peterheinrich/ZHAW_DFF_RPI_Network_Lab_Board/design/90-Ohm-Impedance.png

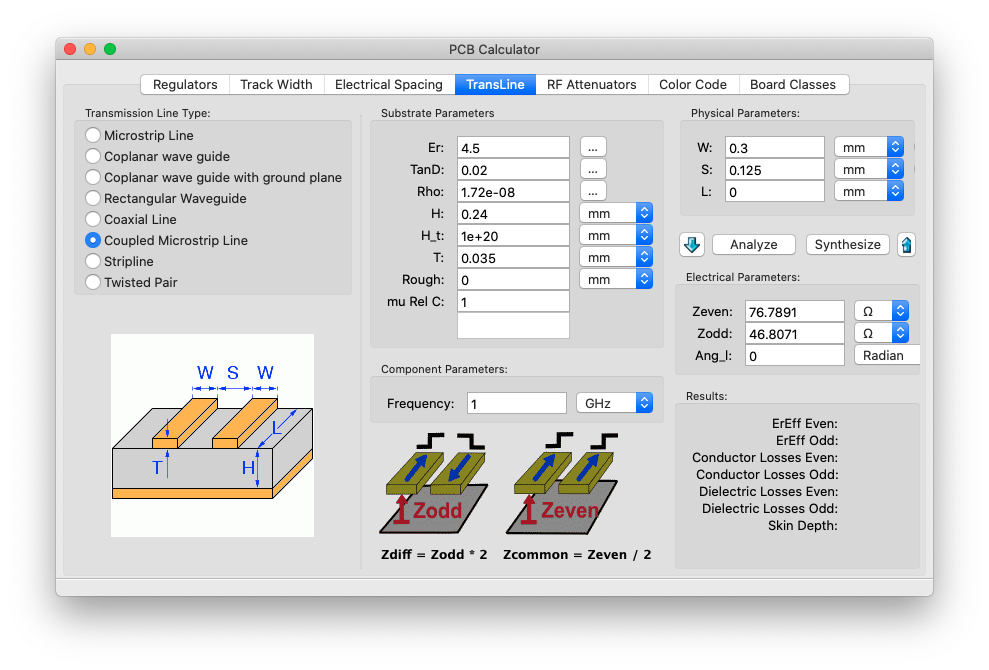
design/90-Ohm-Impedance.png
