peterheinrich/ZHAW_DFF_RPI_Network_Lab_Board/ecad/DSI.sch

## KiCad design ecad/DSI.sch (2020-12-07)

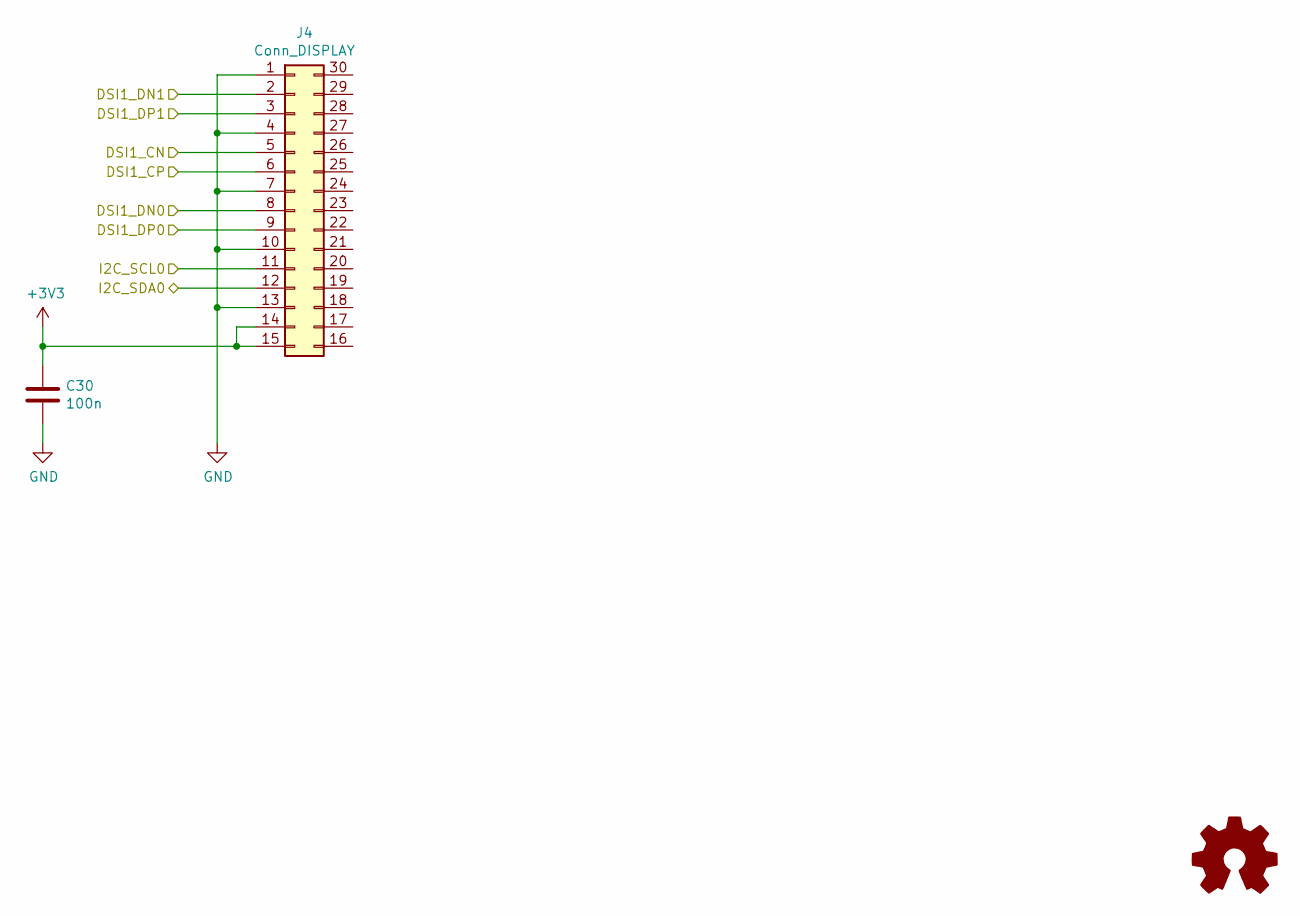
[picture p34: schematic DSI.sch]

Parts:
C30: 100n; C_0603_1608Metric; MPN C0603C104M4RACTU
J4: Conn_DISPLAY; 1-1734248-5; MPN 1-1734248-5

Connections:
+3V3: C30.1, J4.14, J4.15
DSI1_CN: J4.5
DSI1_CP: J4.6
DSI1_DN0: J4.8
DSI1_DN1: J4.2
DSI1_DP0: J4.9
DSI1_DP1: J4.3
GND: C30.2, J4.1, J4.4, J4.7, J4.10, J4.13
I2C_SCL0: J4.11
I2C_SDA0: J4.12
