peterheinrich/ZHAW_DFF_RPI_Network_Lab_Board/ecad/ETH0.sch

## KiCad design ecad/ETH0.sch (2020-12-07)

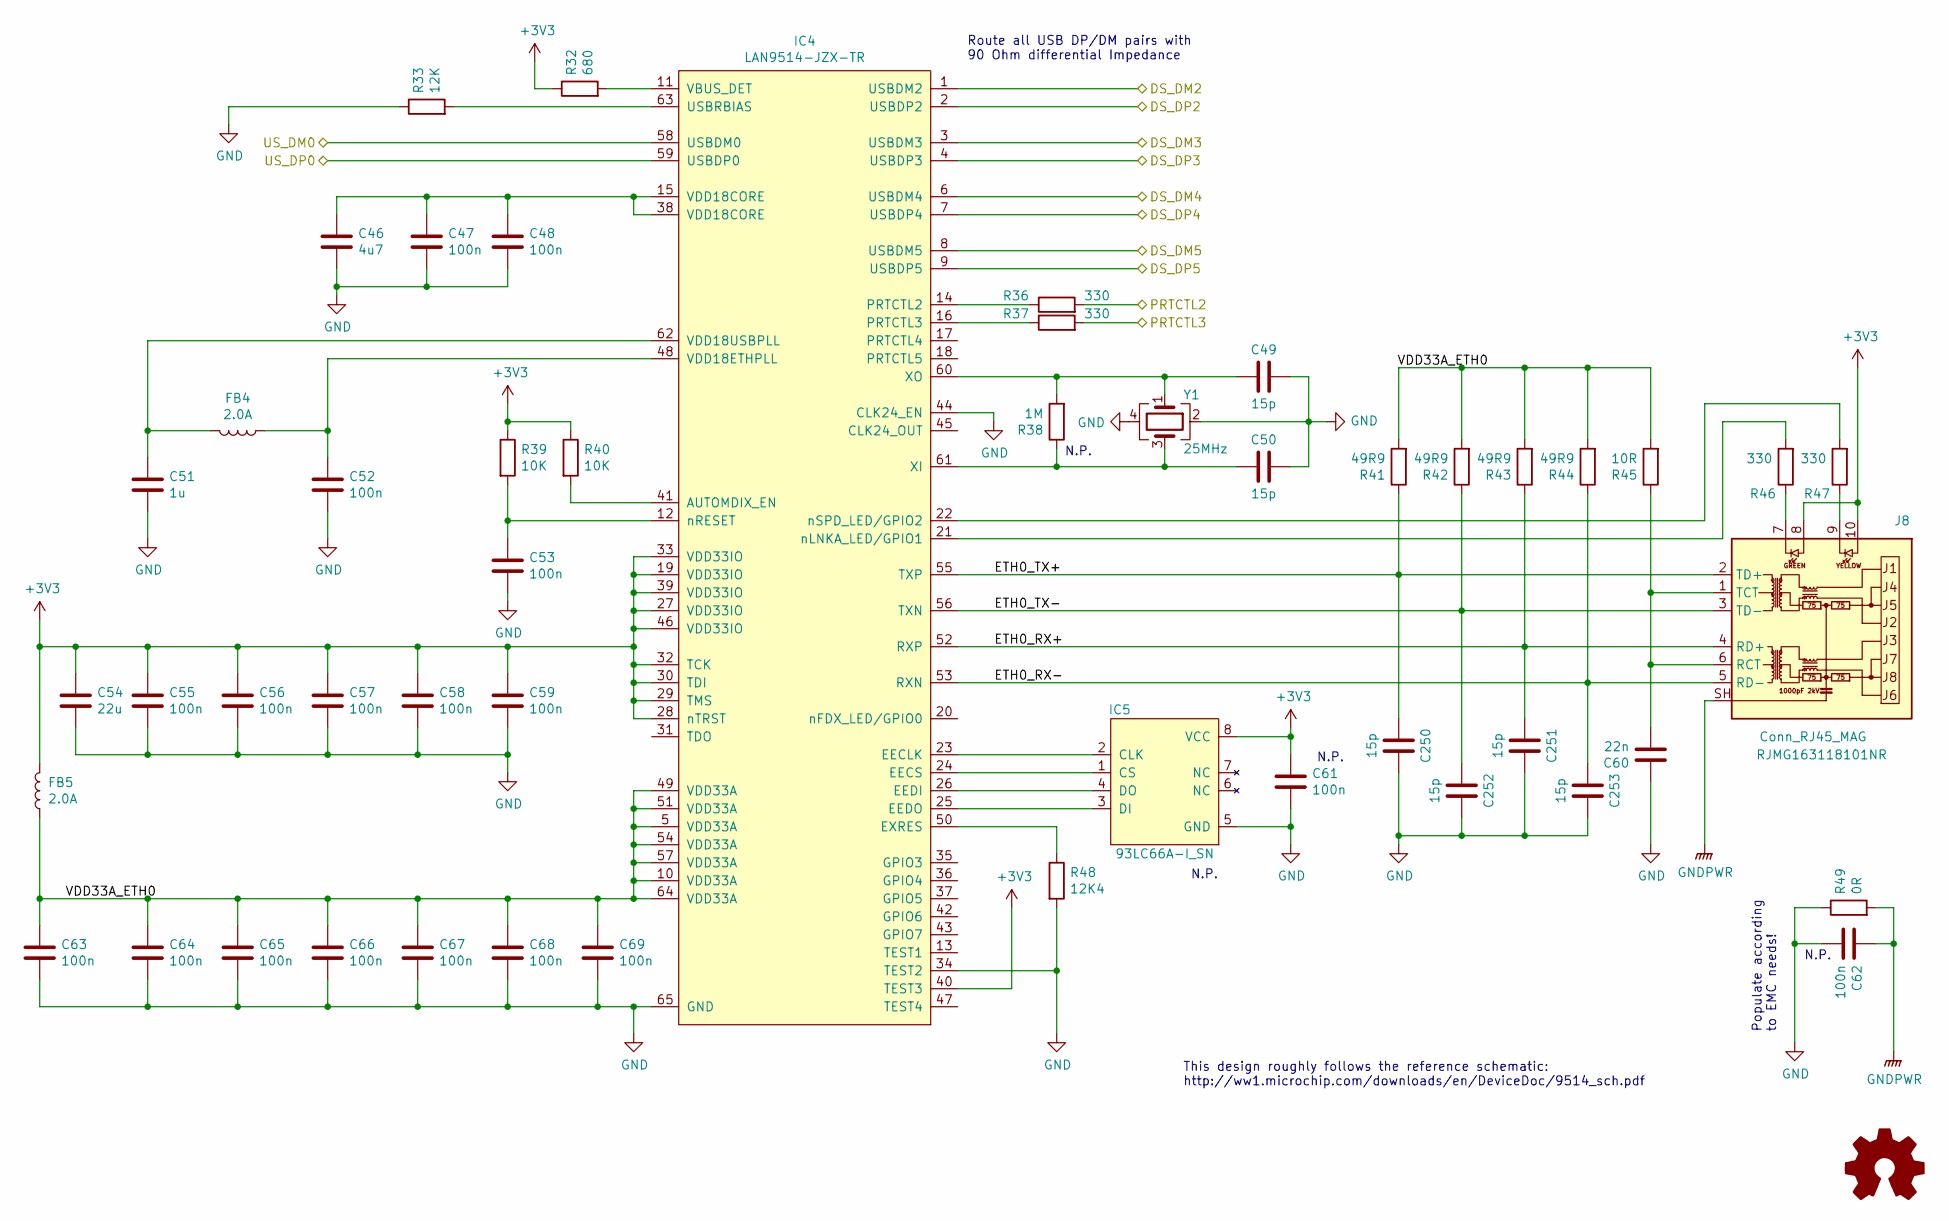
[picture p35: schematic ETH0.sch]

Parts:
C46: 4u7; C_0805_2012Metric; MPN GRM21BR61H475KE51L
C47, C48, C52, C53, C55, C56, C57, C58, C59, C61, C63, C64, C65, C66, C67, C68, C69: 100n; C_0603_1608Metric; MPN C0603C104M4RACTU
C49, C50, C250, C251, C252, C253: 15p; C_0603_1608Metric; MPN C0603C150J5GACTU
C51: 1u; C_0805_2012Metric; MPN C0805C105K3PACTU
C54: 22u; C_0805_2012Metric; MPN C0805C226M9PACTU
C60: 22n; C_0603_1608Metric; MPN C0603C223K1RACTU
C62: 100n; C_0805_2012Metric; MPN C0805C104K5RACTU
FB4, FB5: 2.0A; L_0603_1608Metric_Pad1.05x0.95mm_HandSolder; MPN BLM18PG121SN1D
IC4: LAN9514-JZX-TR; QFN-64-1EP_9x9mm_P0.5mm_EP7.15x7.15mm_ThermalVias; MPN LAN9514-JZX-TR
IC5: 93LC66A-I_SN; SOIC-8_3.9x4.9mm_P1.27mm; MPN 93LC66A-I_SN
J8: Conn_RJ45_MAG; RJMG163118101NR; MPN RJMG163118101NR
R32: 680; R_0603_1608Metric; MPN CRCW0603680RFKEA
R33: 12K; R_0603_1608Metric; MPN CRCW060312K0FKEA
R36, R37, R46, R47: 330; R_0603_1608Metric; MPN CRCW0603330RFKEA
R38: 1M; R_0603_1608Metric; MPN CRCW06031M00FKEA
R39, R40: 10K; R_0603_1608Metric; MPN CRCW060310K0FKEA
R41, R42, R43, R44: 49R9; R_0603_1608Metric; MPN CRCW060349R9FKEA
R45: 10R; R_0603_1608Metric; MPN CRCW060310R0FKEA
R48: 12K4; R_0603_1608Metric; MPN CRCW060312K4FKEA
R49: 0R; R_0805_2012Metric; MPN CRCW08050000Z0EA
Y1: 25MHz; Crystal_SMD_Abracon_ABM8G-4Pin_3.2x2.5mm; MPN LFXTAL055299

Connections:
+3V3: C54.1, C55.1, C56.1, C57.1, C58.1, C59.1, C61.1, FB5.2, IC4.19 (VDD33IO), IC4.27 (VDD33IO), IC4.28 (nTRST), IC4.29 (TMS), IC4.30 (TDI), IC4.32 (TCK), IC4.33 (VDD33IO), IC4.39 (VDD33IO), IC4.40 (TEST3), IC4.46 (VDD33IO), IC5.8 (VCC), J8.8, J8.10, R32.1, R39.1, R40.1
DS_DM2: IC4.1 (USBDM2)
DS_DM3: IC4.3 (USBDM3)
DS_DM4: IC4.6 (USBDM4)
DS_DM5: IC4.8 (USBDM5)
DS_DP2: IC4.2 (USBDP2)
DS_DP3: IC4.4 (USBDP3)
DS_DP4: IC4.7 (USBDP4)
DS_DP5: IC4.9 (USBDP5)
ETH0_RX+: C251.2, IC4.52 (RXP), J8.4 (RD+), R43.1
ETH0_RX-: C253.2, IC4.53 (RXN), J8.5 (RD-), R44.1
ETH0_TX+: C250.2, IC4.55 (TXP), J8.2 (TD+), R41.1
ETH0_TX-: C252.2, IC4.56 (TXN), J8.3 (TD-), R42.1
GND: C46.2, C47.2, C48.2, C49.1, C50.1, C51.2, C52.2, C53.2, C54.2, C55.2, C56.2, C57.2, C58.2, C59.2, C60.1, C61.2, C62.2, C63.2, C64.2, C65.2, C66.2, C67.2, C68.2, C69.2, C250.1, C251.1, C252.1, C253.1, IC4.34 (TEST2), IC4.44 (CLK24_EN), IC4.65 (GND), IC5.5 (GND), R33.1, R48.2, R49.1, Y1.2, Y1.4
GNDPWR: C62.1, J8.SH, R49.2
unnamed: C46.1, C47.1, C48.1, IC4.15 (VDD18CORE), IC4.38 (VDD18CORE)
unnamed: C49.2, IC4.60 (XO), R38.2, Y1.1
unnamed: C50.2, IC4.61 (XI), R38.1, Y1.3
unnamed: C51.1, FB4.2, IC4.62 (VDD18USBPLL)
unnamed: C52.1, FB4.1, IC4.48 (VDD18ETHPLL)
unnamed: C53.1, IC4.12 (nRESET), R39.2
unnamed: C60.2, J8.1 (TCT), J8.6 (RCT), R45.1
unnamed: IC4.11 (VBUS_DET), R32.2
unnamed: IC4.14 (PRTCTL2), R36.1
unnamed: IC4.16 (PRTCTL3), R37.1
unnamed: IC4.21 (nLNKA_LED/GPIO1), R46.2
unnamed: IC4.22 (nSPD_LED/GPIO2), R47.2
unnamed: IC4.23 (EECLK), IC5.2 (CLK)
unnamed: IC4.24 (EECS), IC5.1 (CS)
unnamed: IC4.25 (EEDO), IC5.3 (DI)
unnamed: IC4.26 (EEDI), IC5.4 (DO)
unnamed: IC4.41 (AUTOMDIX_EN), R40.2
unnamed: IC4.50 (EXRES), R48.1
unnamed: IC4.63 (USBRBIAS), R33.2
unnamed: J8.7, R46.1
unnamed: J8.9, R47.1
PRTCTL2: R36.2
PRTCTL3: R37.2
US_DM0: IC4.58 (USBDM0)
US_DP0: IC4.59 (USBDP0)
VDD33A_ETH0: C63.1, C64.1, C65.1, C66.1, C67.1, C68.1, C69.1, FB5.1, IC4.5 (VDD33A), IC4.10 (VDD33A), IC4.49 (VDD33A), IC4.51 (VDD33A), IC4.54 (VDD33A), IC4.57 (VDD33A), IC4.64 (VDD33A), R41.2, R42.2, R43.2, R44.2, R45.2

Notes on the sheet:
N.P.
Route all USB DP/DM pairs with 90 Ohm differential Impedance
This design roughly follows the reference schematic: http://ww1.microchip.com/downloads/en/DeviceDoc/9514_sch.pdf
Populate according to EMC needs!
