peterheinrich/ZHAW_DFF_RPI_Network_Lab_Board/ecad/ETH1.sch

## KiCad design ecad/ETH1.sch (2020-12-07)

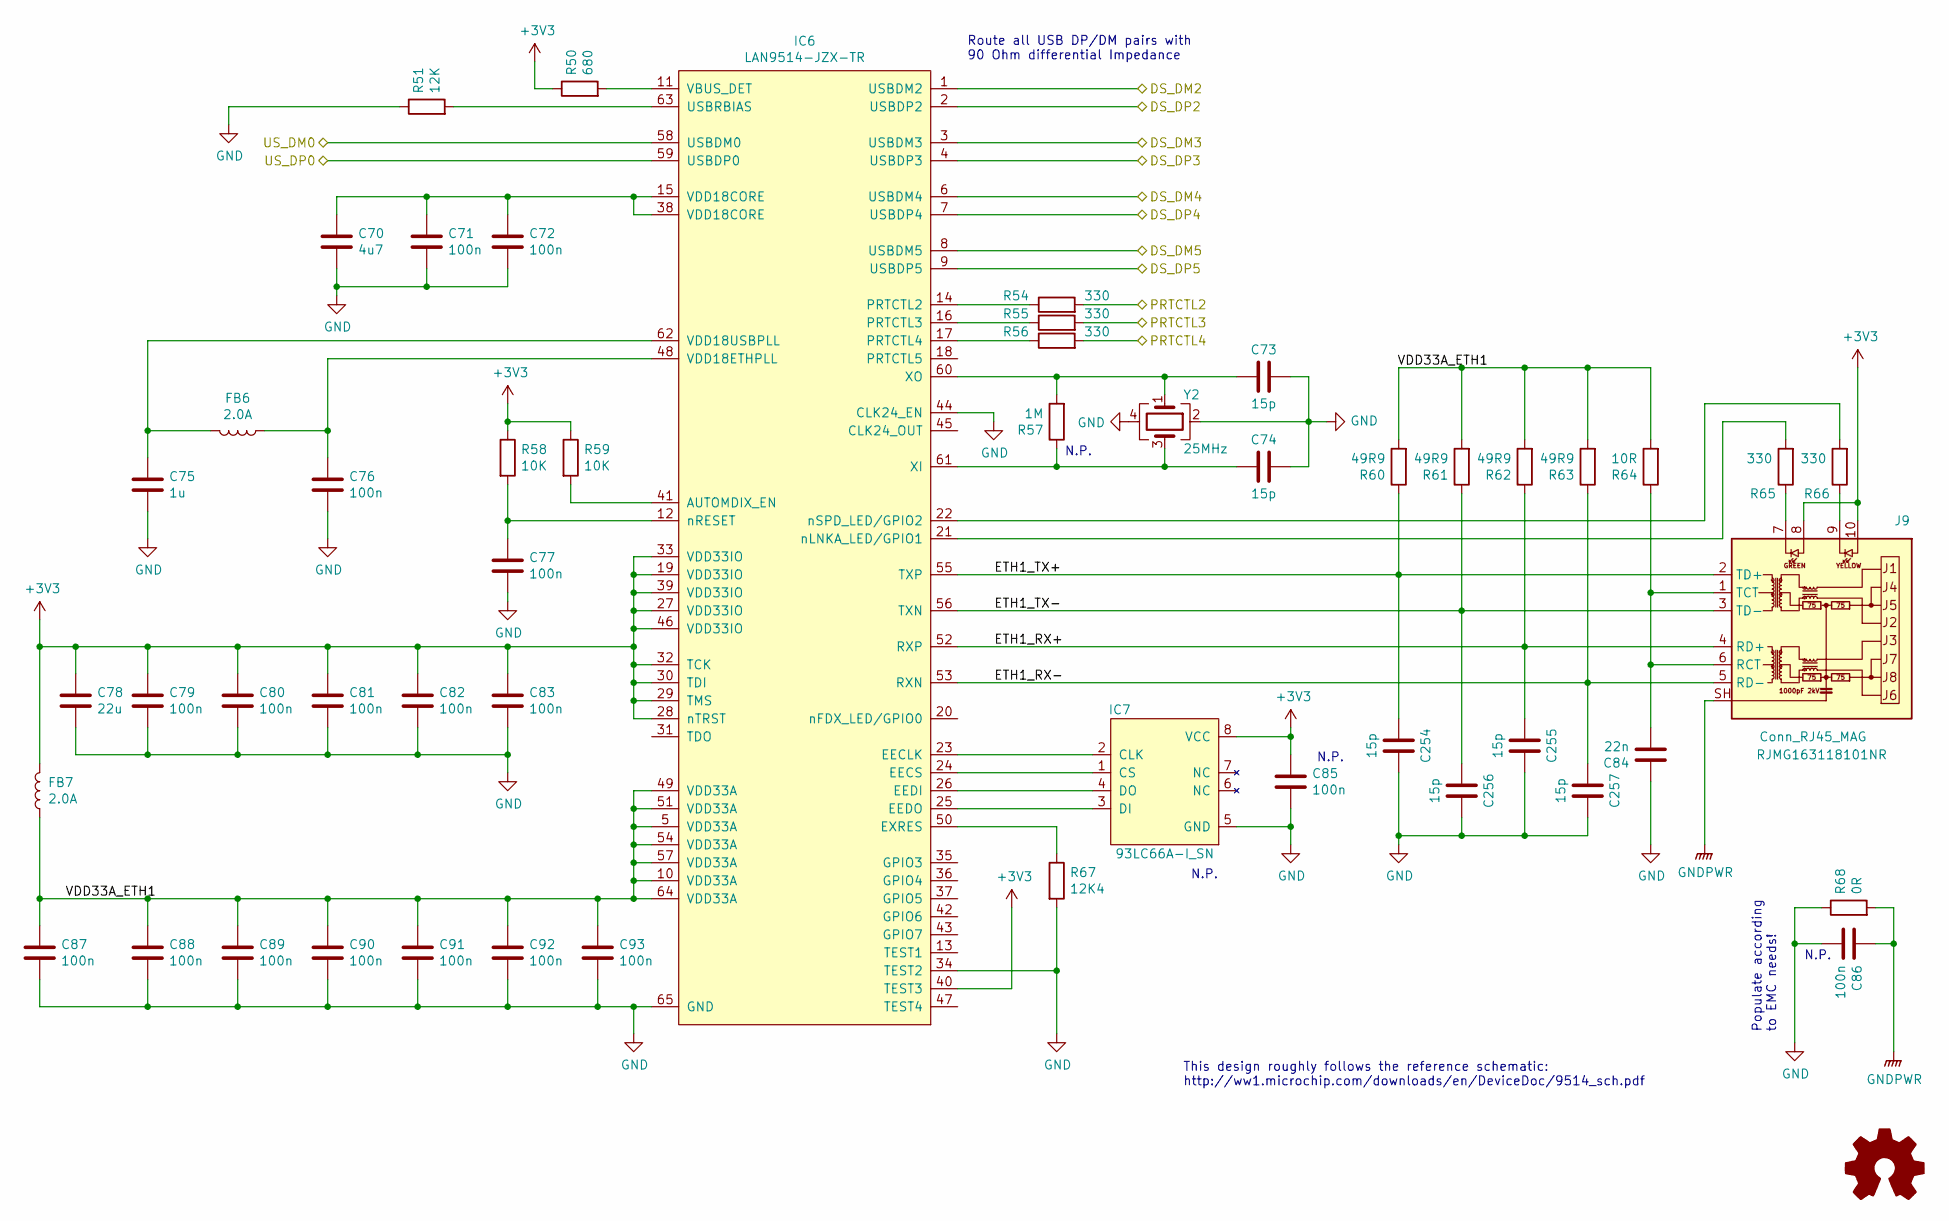
[picture p36: schematic ETH1.sch]

Parts:
C70: 4u7; C_0805_2012Metric; MPN GRM21BR61H475KE51L
C71, C72, C76, C77, C79, C80, C81, C82, C83, C85, C87, C88, C89, C90, C91, C92, C93: 100n; C_0603_1608Metric; MPN C0603C104M4RACTU
C73, C74, C254, C255, C256, C257: 15p; C_0603_1608Metric; MPN C0603C150J5GACTU
C75: 1u; C_0805_2012Metric; MPN C0805C105K3PACTU
C78: 22u; C_0805_2012Metric; MPN C0805C226M9PACTU
C84: 22n; C_0603_1608Metric; MPN C0603C223K1RACTU
C86: 100n; C_0805_2012Metric; MPN C0805C104K5RACTU
FB6, FB7: 2.0A; L_0603_1608Metric_Pad1.05x0.95mm_HandSolder; MPN BLM18PG121SN1D
IC6: LAN9514-JZX-TR; QFN-64-1EP_9x9mm_P0.5mm_EP7.15x7.15mm_ThermalVias; MPN LAN9514-JZX-TR
IC7: 93LC66A-I_SN; SOIC-8_3.9x4.9mm_P1.27mm; MPN 93LC66A-I_SN
J9: Conn_RJ45_MAG; RJMG163118101NR; MPN RJMG163118101NR
R50: 680; R_0603_1608Metric; MPN CRCW0603680RFKEA
R51: 12K; R_0603_1608Metric; MPN CRCW060312K0FKEA
R54, R55, R56, R65, R66: 330; R_0603_1608Metric; MPN CRCW0603330RFKEA
R57: 1M; R_0603_1608Metric; MPN CRCW06031M00FKEA
R58, R59: 10K; R_0603_1608Metric; MPN CRCW060310K0FKEA
R60, R61, R62, R63: 49R9; R_0603_1608Metric; MPN CRCW060349R9FKEA
R64: 10R; R_0603_1608Metric; MPN CRCW060310R0FKEA
R67: 12K4; R_0603_1608Metric; MPN CRCW060312K4FKEA
R68: 0R; R_0805_2012Metric; MPN CRCW08050000Z0EA
Y2: 25MHz; Crystal_SMD_Abracon_ABM8G-4Pin_3.2x2.5mm; MPN LFXTAL055299

Connections:
+3V3: C78.1, C79.1, C80.1, C81.1, C82.1, C83.1, C85.1, FB7.2, IC6.19 (VDD33IO), IC6.27 (VDD33IO), IC6.28 (nTRST), IC6.29 (TMS), IC6.30 (TDI), IC6.32 (TCK), IC6.33 (VDD33IO), IC6.39 (VDD33IO), IC6.40 (TEST3), IC6.46 (VDD33IO), IC7.8 (VCC), J9.8, J9.10, R50.1, R58.1, R59.1
DS_DM2: IC6.1 (USBDM2)
DS_DM3: IC6.3 (USBDM3)
DS_DM4: IC6.6 (USBDM4)
DS_DM5: IC6.8 (USBDM5)
DS_DP2: IC6.2 (USBDP2)
DS_DP3: IC6.4 (USBDP3)
DS_DP4: IC6.7 (USBDP4)
DS_DP5: IC6.9 (USBDP5)
ETH1_RX+: C255.2, IC6.52 (RXP), J9.4 (RD+), R62.1
ETH1_RX-: C257.2, IC6.53 (RXN), J9.5 (RD-), R63.1
ETH1_TX+: C254.2, IC6.55 (TXP), J9.2 (TD+), R60.1
ETH1_TX-: C256.2, IC6.56 (TXN), J9.3 (TD-), R61.1
GND: C70.2, C71.2, C72.2, C73.1, C74.1, C75.2, C76.2, C77.2, C78.2, C79.2, C80.2, C81.2, C82.2, C83.2, C84.1, C85.2, C86.2, C87.2, C88.2, C89.2, C90.2, C91.2, C92.2, C93.2, C254.1, C255.1, C256.1, C257.1, IC6.34 (TEST2), IC6.44 (CLK24_EN), IC6.65 (GND), IC7.5 (GND), R51.1, R67.2, R68.1, Y2.2, Y2.4
GNDPWR: C86.1, J9.SH, R68.2
unnamed: C70.1, C71.1, C72.1, IC6.15 (VDD18CORE), IC6.38 (VDD18CORE)
unnamed: C73.2, IC6.60 (XO), R57.2, Y2.1
unnamed: C74.2, IC6.61 (XI), R57.1, Y2.3
unnamed: C75.1, FB6.2, IC6.62 (VDD18USBPLL)
unnamed: C76.1, FB6.1, IC6.48 (VDD18ETHPLL)
unnamed: C77.1, IC6.12 (nRESET), R58.2
unnamed: C84.2, J9.1 (TCT), J9.6 (RCT), R64.1
unnamed: IC6.11 (VBUS_DET), R50.2
unnamed: IC6.14 (PRTCTL2), R54.1
unnamed: IC6.16 (PRTCTL3), R55.1
unnamed: IC6.17 (PRTCTL4), R56.1
unnamed: IC6.21 (nLNKA_LED/GPIO1), R65.2
unnamed: IC6.22 (nSPD_LED/GPIO2), R66.2
unnamed: IC6.23 (EECLK), IC7.2 (CLK)
unnamed: IC6.24 (EECS), IC7.1 (CS)
unnamed: IC6.25 (EEDO), IC7.3 (DI)
unnamed: IC6.26 (EEDI), IC7.4 (DO)
unnamed: IC6.41 (AUTOMDIX_EN), R59.2
unnamed: IC6.50 (EXRES), R67.1
unnamed: IC6.63 (USBRBIAS), R51.2
unnamed: J9.7, R65.1
unnamed: J9.9, R66.1
PRTCTL2: R54.2
PRTCTL3: R55.2
PRTCTL4: R56.2
US_DM0: IC6.58 (USBDM0)
US_DP0: IC6.59 (USBDP0)
VDD33A_ETH1: C87.1, C88.1, C89.1, C90.1, C91.1, C92.1, C93.1, FB7.1, IC6.5 (VDD33A), IC6.10 (VDD33A), IC6.49 (VDD33A), IC6.51 (VDD33A), IC6.54 (VDD33A), IC6.57 (VDD33A), IC6.64 (VDD33A), R60.2, R61.2, R62.2, R63.2, R64.2

Notes on the sheet:
N.P.
Route all USB DP/DM pairs with 90 Ohm differential Impedance
This design roughly follows the reference schematic: http://ww1.microchip.com/downloads/en/DeviceDoc/9514_sch.pdf
Populate according to EMC needs!
