peterheinrich/ZHAW_DFF_RPI_Network_Lab_Board/ecad/ETH2.sch

## KiCad design ecad/ETH2.sch (2020-12-07)

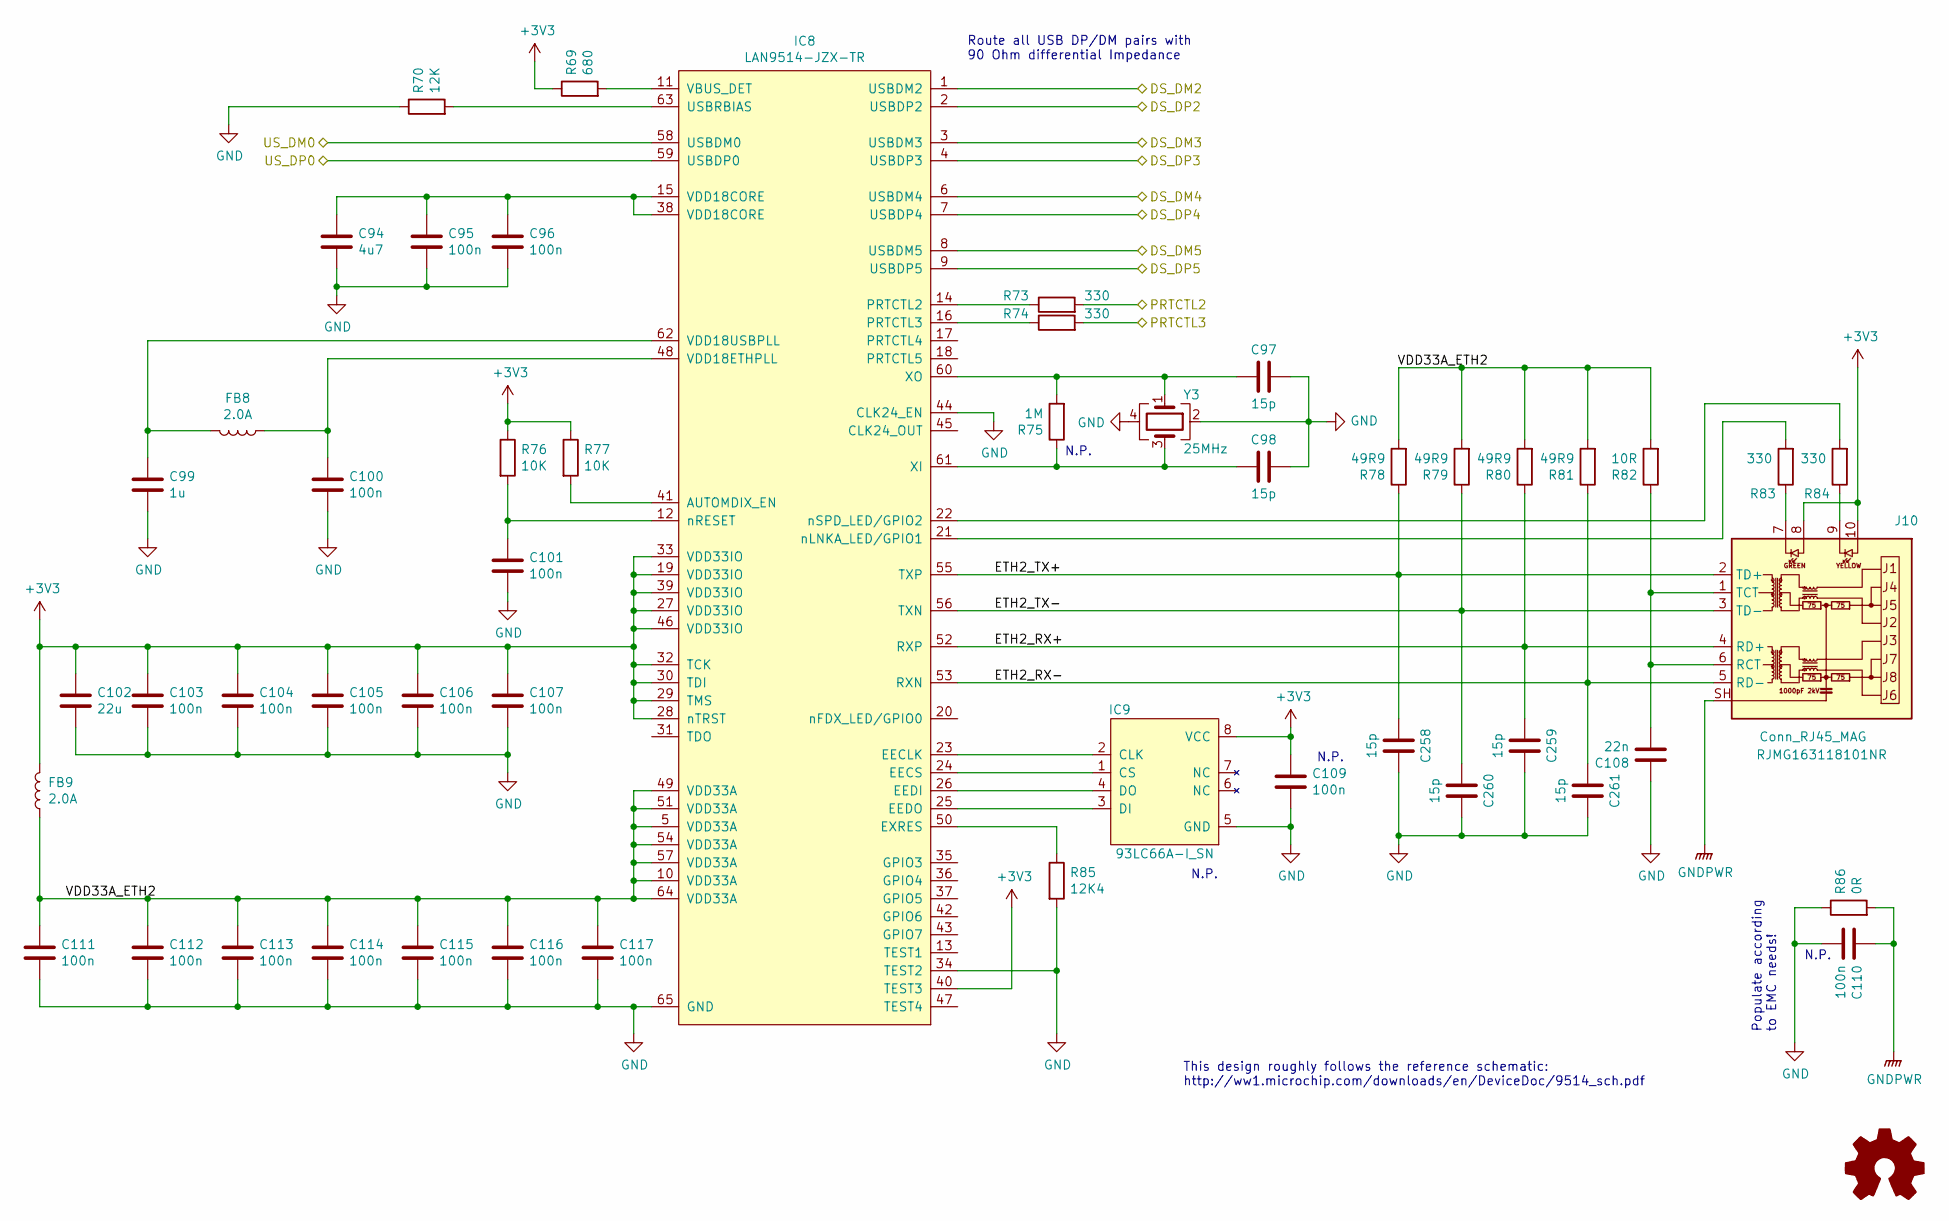
[picture p37: schematic ETH2.sch]

Parts:
C94: 4u7; C_0805_2012Metric; MPN GRM21BR61H475KE51L
C95, C96, C100, C101, C103, C104, C105, C106, C107, C109, C111, C112, C113, C114, C115, C116, C117: 100n; C_0603_1608Metric; MPN C0603C104M4RACTU
C97, C98, C258, C259, C260, C261: 15p; C_0603_1608Metric; MPN C0603C150J5GACTU
C99: 1u; C_0805_2012Metric; MPN C0805C105K3PACTU
C102: 22u; C_0805_2012Metric; MPN C0805C226M9PACTU
C108: 22n; C_0603_1608Metric; MPN C0603C223K1RACTU
C110: 100n; C_0805_2012Metric; MPN C0805C104K5RACTU
FB8, FB9: 2.0A; L_0603_1608Metric_Pad1.05x0.95mm_HandSolder; MPN BLM18PG121SN1D
IC8: LAN9514-JZX-TR; QFN-64-1EP_9x9mm_P0.5mm_EP7.15x7.15mm_ThermalVias; MPN LAN9514-JZX-TR
IC9: 93LC66A-I_SN; SOIC-8_3.9x4.9mm_P1.27mm; MPN 93LC66A-I_SN
J10: Conn_RJ45_MAG; RJMG163118101NR; MPN RJMG163118101NR
R69: 680; R_0603_1608Metric; MPN CRCW0603680RFKEA
R70: 12K; R_0603_1608Metric; MPN CRCW060312K0FKEA
R73, R74, R83, R84: 330; R_0603_1608Metric; MPN CRCW0603330RFKEA
R75: 1M; R_0603_1608Metric; MPN CRCW06031M00FKEA
R76, R77: 10K; R_0603_1608Metric; MPN CRCW060310K0FKEA
R78, R79, R80, R81: 49R9; R_0603_1608Metric; MPN CRCW060349R9FKEA
R82: 10R; R_0603_1608Metric; MPN CRCW060310R0FKEA
R85: 12K4; R_0603_1608Metric; MPN CRCW060312K4FKEA
R86: 0R; R_0805_2012Metric; MPN CRCW08050000Z0EA
Y3: 25MHz; Crystal_SMD_Abracon_ABM8G-4Pin_3.2x2.5mm; MPN LFXTAL055299

Connections:
+3V3: C102.1, C103.1, C104.1, C105.1, C106.1, C107.1, C109.1, FB9.2, IC8.19 (VDD33IO), IC8.27 (VDD33IO), IC8.28 (nTRST), IC8.29 (TMS), IC8.30 (TDI), IC8.32 (TCK), IC8.33 (VDD33IO), IC8.39 (VDD33IO), IC8.40 (TEST3), IC8.46 (VDD33IO), IC9.8 (VCC), J10.8, J10.10, R69.1, R76.1, R77.1
DS_DM2: IC8.1 (USBDM2)
DS_DM3: IC8.3 (USBDM3)
DS_DM4: IC8.6 (USBDM4)
DS_DM5: IC8.8 (USBDM5)
DS_DP2: IC8.2 (USBDP2)
DS_DP3: IC8.4 (USBDP3)
DS_DP4: IC8.7 (USBDP4)
DS_DP5: IC8.9 (USBDP5)
ETH2_RX+: C259.2, IC8.52 (RXP), J10.4 (RD+), R80.1
ETH2_RX-: C261.2, IC8.53 (RXN), J10.5 (RD-), R81.1
ETH2_TX+: C258.2, IC8.55 (TXP), J10.2 (TD+), R78.1
ETH2_TX-: C260.2, IC8.56 (TXN), J10.3 (TD-), R79.1
GND: C94.2, C95.2, C96.2, C97.1, C98.1, C99.2, C100.2, C101.2, C102.2, C103.2, C104.2, C105.2, C106.2, C107.2, C108.1, C109.2, C110.2, C111.2, C112.2, C113.2, C114.2, C115.2, C116.2, C117.2, C258.1, C259.1, C260.1, C261.1, IC8.34 (TEST2), IC8.44 (CLK24_EN), IC8.65 (GND), IC9.5 (GND), R70.1, R85.2, R86.1, Y3.2, Y3.4
GNDPWR: C110.1, J10.SH, R86.2
unnamed: C94.1, C95.1, C96.1, IC8.15 (VDD18CORE), IC8.38 (VDD18CORE)
unnamed: C97.2, IC8.60 (XO), R75.2, Y3.1
unnamed: C98.2, IC8.61 (XI), R75.1, Y3.3
unnamed: C99.1, FB8.2, IC8.62 (VDD18USBPLL)
unnamed: C100.1, FB8.1, IC8.48 (VDD18ETHPLL)
unnamed: C101.1, IC8.12 (nRESET), R76.2
unnamed: C108.2, J10.1 (TCT), J10.6 (RCT), R82.1
unnamed: IC8.11 (VBUS_DET), R69.2
unnamed: IC8.14 (PRTCTL2), R73.1
unnamed: IC8.16 (PRTCTL3), R74.1
unnamed: IC8.21 (nLNKA_LED/GPIO1), R83.2
unnamed: IC8.22 (nSPD_LED/GPIO2), R84.2
unnamed: IC8.23 (EECLK), IC9.2 (CLK)
unnamed: IC8.24 (EECS), IC9.1 (CS)
unnamed: IC8.25 (EEDO), IC9.3 (DI)
unnamed: IC8.26 (EEDI), IC9.4 (DO)
unnamed: IC8.41 (AUTOMDIX_EN), R77.2
unnamed: IC8.50 (EXRES), R85.1
unnamed: IC8.63 (USBRBIAS), R70.2
unnamed: J10.7, R83.1
unnamed: J10.9, R84.1
PRTCTL2: R73.2
PRTCTL3: R74.2
US_DM0: IC8.58 (USBDM0)
US_DP0: IC8.59 (USBDP0)
VDD33A_ETH2: C111.1, C112.1, C113.1, C114.1, C115.1, C116.1, C117.1, FB9.1, IC8.5 (VDD33A), IC8.10 (VDD33A), IC8.49 (VDD33A), IC8.51 (VDD33A), IC8.54 (VDD33A), IC8.57 (VDD33A), IC8.64 (VDD33A), R78.2, R79.2, R80.2, R81.2, R82.2

Notes on the sheet:
N.P.
Route all USB DP/DM pairs with 90 Ohm differential Impedance
This design roughly follows the reference schematic: http://ww1.microchip.com/downloads/en/DeviceDoc/9514_sch.pdf
Populate according to EMC needs!
