peterheinrich/ZHAW_DFF_RPI_Network_Lab_Board/ecad/HDMI.sch

## KiCad design ecad/HDMI.sch (2020-12-07)

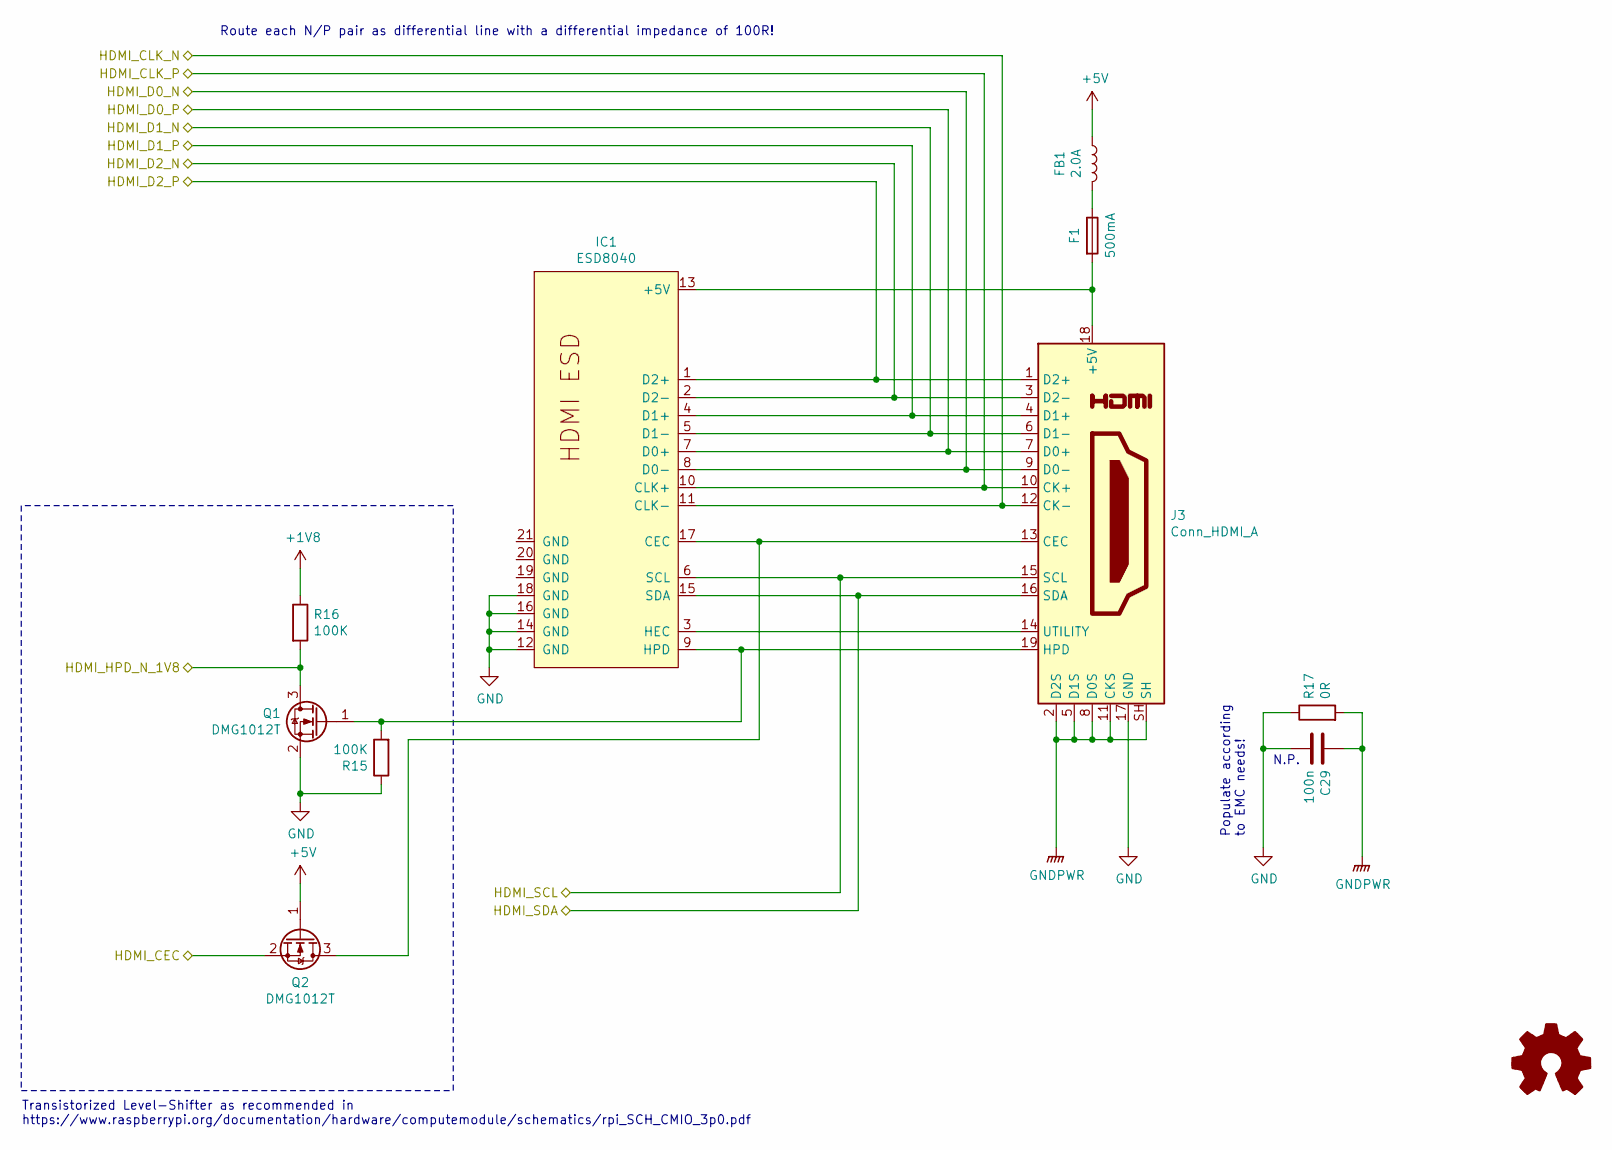
[picture p38: schematic HDMI.sch]

Parts:
C29: 100n; C_0805_2012Metric; MPN C0805C104K5RACTU
F1: 500mA; Fuse_1206_3216Metric; MPN 1206L050YR
FB1: 2.0A; L_0603_1608Metric_Pad1.05x0.95mm_HandSolder; MPN BLM18PG121SN1D
IC1: ESD8040; MPN ESD8040MUTAG
J3: Conn_HDMI_A; 47151-1051; MPN 47151-1051
Q1, Q2: DMG1012T; SOT-532; MPN DMG1012T-7
R15, R16: 100K; R_0603_1608Metric; MPN CRCW0603100KFKEA
R17: 0R; R_0805_2012Metric; MPN CRCW08050000Z0EA

Connections:
+1V8: R16.1
+5V: FB1.1, Q2.1 (G)
GND: C29.2, IC1.12 (GND), IC1.14 (GND), IC1.16 (GND), IC1.18 (GND), J3.17 (GND), Q1.2 (S), R15.1, R17.1
GNDPWR: C29.1, J3.2 (D2S), J3.5 (D1S), J3.8 (D0S), J3.11 (CKS), J3.SH, R17.2
HDMI_CEC: Q2.2 (S)
HDMI_CLK_N: IC1.11 (CLK-), J3.12 (CK-)
HDMI_CLK_P: IC1.10 (CLK+), J3.10 (CK+)
HDMI_D0_N: IC1.8 (D0-), J3.9 (D0-)
HDMI_D0_P: IC1.7 (D0+), J3.7 (D0+)
HDMI_D1_N: IC1.5 (D1-), J3.6 (D1-)
HDMI_D1_P: IC1.4 (D1+), J3.4 (D1+)
HDMI_D2_N: IC1.2 (D2-), J3.3 (D2-)
HDMI_D2_P: IC1.1 (D2+), J3.1 (D2+)
HDMI_HPD_N_1V8: Q1.3 (D), R16.2
HDMI_SCL: IC1.6 (SCL), J3.15 (SCL)
HDMI_SDA: IC1.15 (SDA), J3.16 (SDA)
unnamed: F1.1, FB1.2
unnamed: F1.2, IC1.13 (+5V), J3.18 (+5V)
unnamed: IC1.3 (HEC), J3.14 (UTILITY)
unnamed: IC1.9 (HPD), J3.19 (HPD), Q1.1 (G), R15.2
unnamed: IC1.17 (CEC), J3.13 (CEC), Q2.3 (D)

Notes on the sheet:
Populate according to EMC needs!
N.P.
Route each N/P pair as differential line with a differential impedance of 100R!
Transistorized Level-Shifter as recommended in https://www.raspberrypi.org/documentation/hardware/computemodule/schematics/rpi_SCH_CMIO_3p0.pdf
