peterheinrich/ZHAW_DFF_RPI_Network_Lab_Board/ecad/MS0.sch

## KiCad design ecad/MS0.sch (2020-12-07)

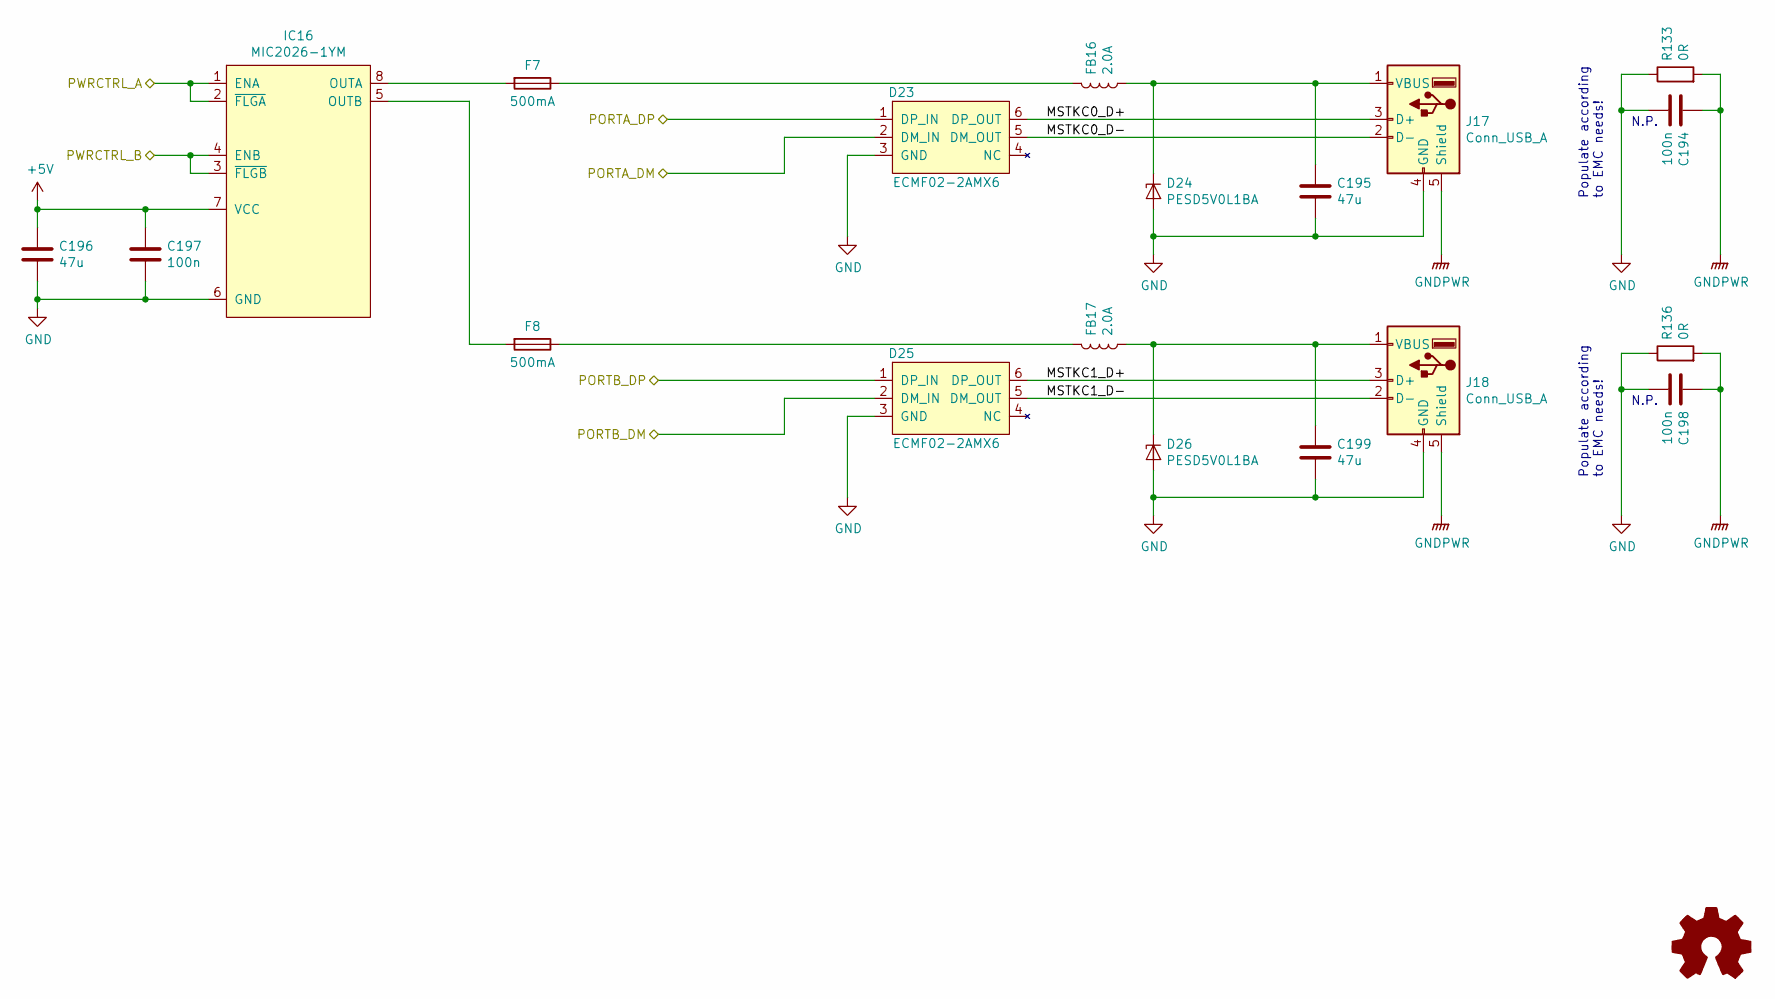
[picture p39: schematic MS0.sch]

Parts:
C194, C198: 100n; C_0805_2012Metric; MPN C0805C104K5RACTU
C195, C196, C199: 47u; C_0805_2012Metric; MPN GRM21BR60J476ME15L
C197: 100n; C_0603_1608Metric; MPN C0603C104M4RACTU
D23, D25: ECMF02-2AMX6; ST_UQFN-6L_1.5x1.7mm_Pitch0.5mm; MPN ECMF02-2AMX6
D24, D26: PESD5V0L1BA; D_SOD-323_HandSoldering; MPN PESD5V0L1BA,115
F7, F8: 500mA; Fuse_1206_3216Metric; MPN 1206L050YR
FB16, FB17: 2.0A; L_0603_1608Metric_Pad1.05x0.95mm_HandSolder; MPN BLM18PG121SN1D
IC16: MIC2026-1YM; SOIC-8_3.9x4.9mm_P1.27mm; MPN MIC2026-1YM
J17, J18: Conn_USB_A; 1734366-1; MPN 1734366-1
R133, R136: 0R; R_0805_2012Metric; MPN CRCW08050000Z0EA

Connections:
+5V: C196.1, C197.1, IC16.7 (VCC)
GND: C194.2, C195.2, C196.2, C197.2, C198.2, C199.2, D23.3 (GND), D24.2 (A), D25.3 (GND), D26.2 (A), IC16.6 (GND), J17.4 (GND), J18.4 (GND), R133.1, R136.1
GNDPWR: C194.1, C198.1, J17.5 (Shield), J18.5 (Shield), R133.2, R136.2
MSTKC0_D+: D23.6 (DP_OUT), J17.3 (D+)
MSTKC0_D-: D23.5 (DM_OUT), J17.2 (D-)
MSTKC1_D+: D25.6 (DP_OUT), J18.3 (D+)
MSTKC1_D-: D25.5 (DM_OUT), J18.2 (D-)
unnamed: C195.1, D24.1 (K1), FB16.1, J17.1 (VBUS)
unnamed: C199.1, D26.1 (K1), FB17.1, J18.1 (VBUS)
unnamed: F7.1, FB16.2
unnamed: F7.2, IC16.8 (OUTA)
unnamed: F8.1, FB17.2
unnamed: F8.2, IC16.5 (OUTB)
PORTA_DM: D23.2 (DM_IN)
PORTA_DP: D23.1 (DP_IN)
PORTB_DM: D25.2 (DM_IN)
PORTB_DP: D25.1 (DP_IN)
PWRCTRL_A: IC16.1 (ENA), IC16.2 (~FLGA)
PWRCTRL_B: IC16.3 (~FLGB), IC16.4 (ENB)

Notes on the sheet:
Populate according to EMC needs!
N.P.
