peterheinrich/ZHAW_DFF_RPI_Network_Lab_Board/ecad/MS2.sch

## KiCad design ecad/MS2.sch (2020-12-07)

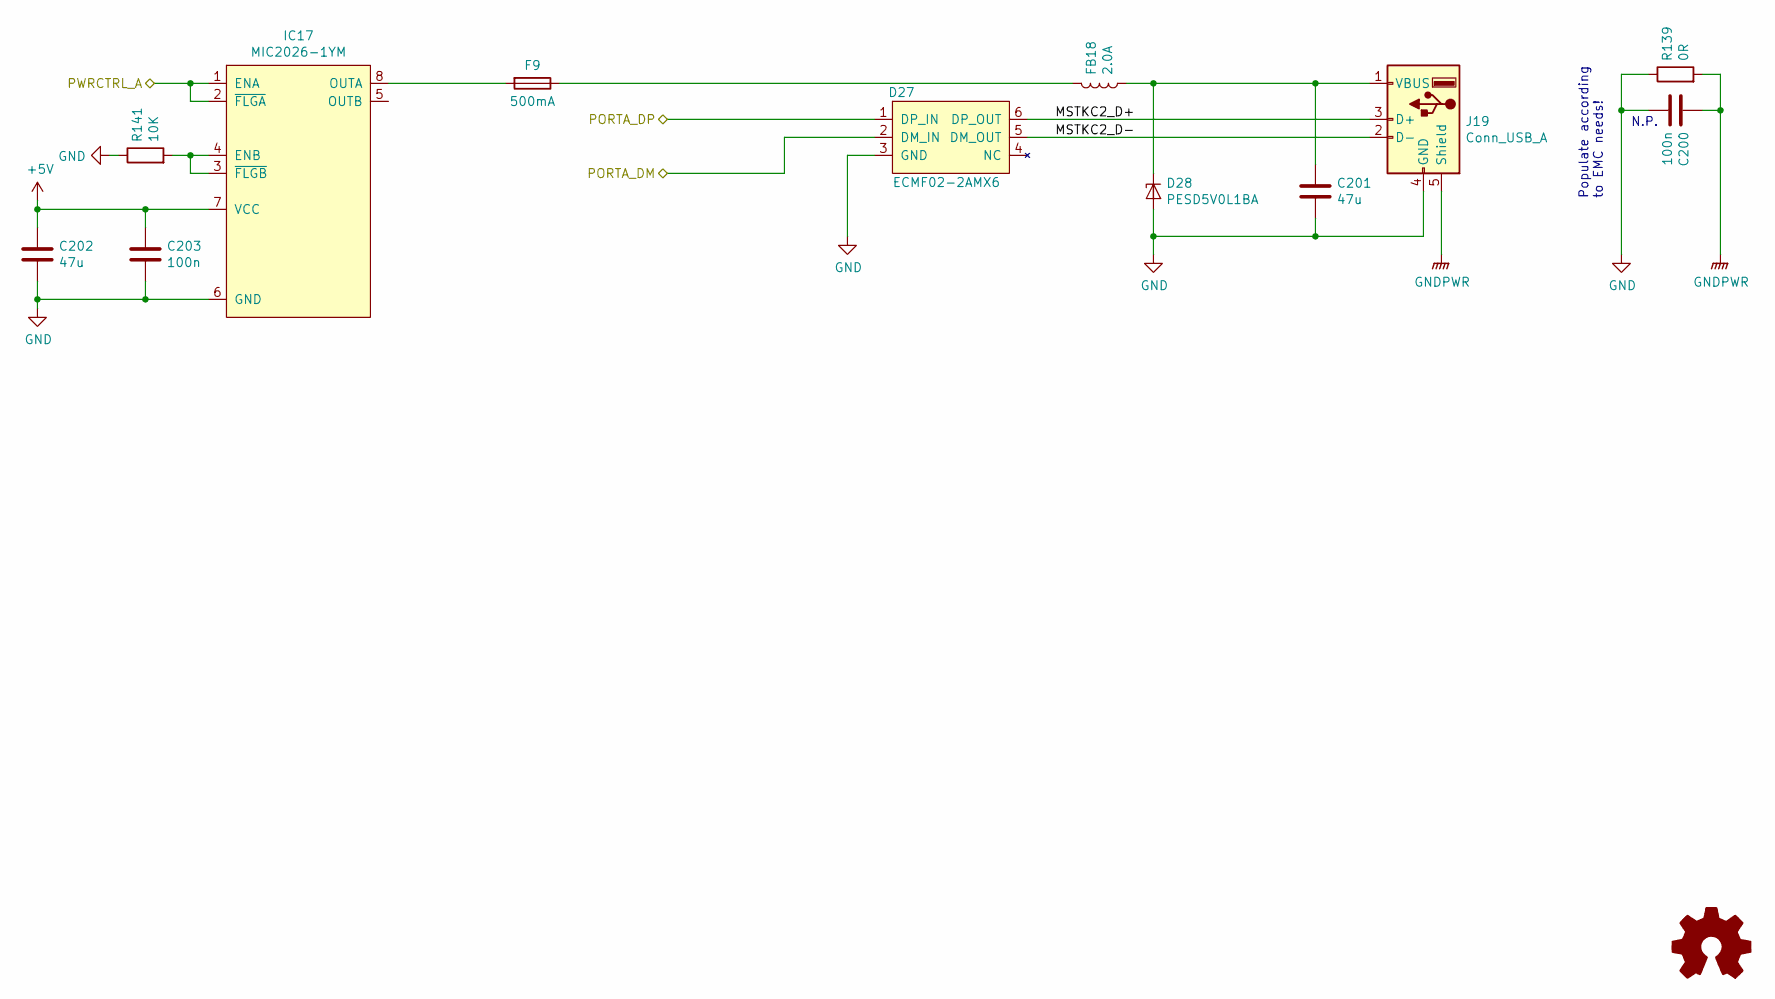
[picture p40: schematic MS2.sch]

Parts:
C200: 100n; C_0805_2012Metric; MPN C0805C104K5RACTU
C201, C202: 47u; C_0805_2012Metric; MPN GRM21BR60J476ME15L
C203: 100n; C_0603_1608Metric; MPN C0603C104M4RACTU
D27: ECMF02-2AMX6; ST_UQFN-6L_1.5x1.7mm_Pitch0.5mm; MPN ECMF02-2AMX6
D28: PESD5V0L1BA; D_SOD-323_HandSoldering; MPN PESD5V0L1BA,115
F9: 500mA; Fuse_1206_3216Metric; MPN 1206L050YR
FB18: 2.0A; L_0603_1608Metric_Pad1.05x0.95mm_HandSolder; MPN BLM18PG121SN1D
IC17: MIC2026-1YM; SOIC-8_3.9x4.9mm_P1.27mm; MPN MIC2026-1YM
J19: Conn_USB_A; 1734366-1; MPN 1734366-1
R139: 0R; R_0805_2012Metric; MPN CRCW08050000Z0EA
R141: 10K; R_0603_1608Metric; MPN CRCW060310K0FKEA

Connections:
+5V: C202.1, C203.1, IC17.7 (VCC)
GND: C200.2, C201.2, C202.2, C203.2, D27.3 (GND), D28.2 (A), IC17.6 (GND), J19.4 (GND), R139.1, R141.1
GNDPWR: C200.1, J19.5 (Shield), R139.2
MSTKC2_D+: D27.6 (DP_OUT), J19.3 (D+)
MSTKC2_D-: D27.5 (DM_OUT), J19.2 (D-)
unnamed: C201.1, D28.1 (K1), FB18.1, J19.1 (VBUS)
unnamed: F9.1, FB18.2
unnamed: F9.2, IC17.8 (OUTA)
unnamed: IC17.3 (~FLGB), IC17.4 (ENB), R141.2
PORTA_DM: D27.2 (DM_IN)
PORTA_DP: D27.1 (DP_IN)
PWRCTRL_A: IC17.1 (ENA), IC17.2 (~FLGA)

Notes on the sheet:
Populate according to EMC needs!
N.P.
