peterheinrich/ZHAW_DFF_RPI_Network_Lab_Board/ecad/PowerSupply0.sch

## KiCad design ecad/PowerSupply0.sch (2020-12-07)

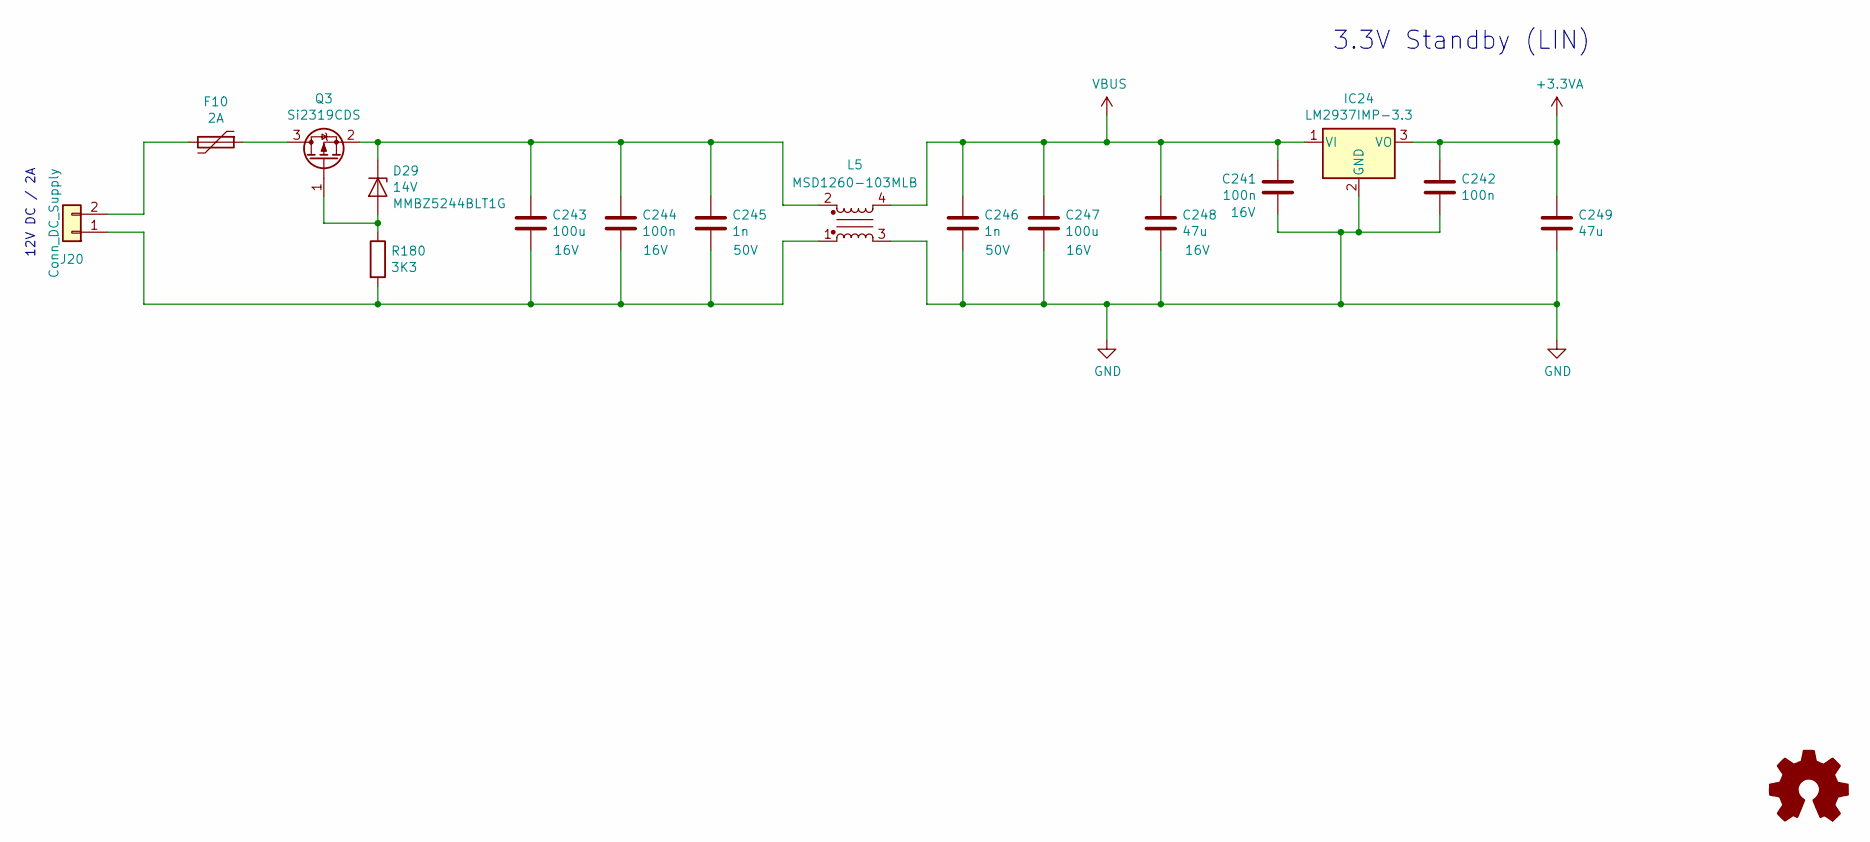
[picture p41: schematic PowerSupply0.sch]

Parts:
C241, C242, C244: 100n; C_0603_1608Metric; MPN C0603C104M4RACTU
C243, C247: 100u; C_1210_3225Metric; MPN C1210C107M4PACTU
C245, C246: 1n; C_0603_1608Metric; MPN C0603C102K5RACTU
C248: 47u; C_1210_3225Metric; MPN GRM32EC81C476KE15L
C249: 47u; C_0805_2012Metric; MPN GRM21BR60J476ME15L
D29: 14V; D_SOT-23_ANK; MPN MMBZ5244BLT1G
F10: 2A; Fuse_1812_4532Metric; MPN 1812L200THPR
IC24: LM2937IMP-3.3; SOT-223-3_TabPin2; MPN LM2937IMP-3.3/NOPB
J20: Conn_DC_Supply; TerminalBlock_bornier-2_P5.08mm; MPN MC24366
L5: MSD1260-103MLB; MPN MSD1260-103MLB
Q3: Si2319CDS; SOT-23; MPN SI2319CDS-T1-GE3
R180: 3K3; R_0603_1608Metric; MPN CRCW06033K30FKEA

Connections:
+3.3VA: C242.1, C249.1, IC24.3 (VO)
GND: C241.2, C242.2, C246.2, C247.2, C248.2, C249.2, IC24.2 (GND), L5.3
unnamed: C243.1, C244.1, C245.1, D29.1 (K), L5.2, Q3.2 (S)
unnamed: C243.2, C244.2, C245.2, J20.1, L5.1, R180.2
unnamed: D29.2 (A), Q3.1 (G), R180.1
unnamed: F10.1, Q3.3 (D)
unnamed: F10.2, J20.2
VBUS: C241.1, C246.1, C247.1, C248.1, IC24.1 (VI), L5.4

Notes on the sheet:
12V DC / 2A
3.3V Standby (LIN)
