peterheinrich/ZHAW_DFF_RPI_Network_Lab_Board/ecad/PowerSupply1.sch

## KiCad design ecad/PowerSupply1.sch (2020-12-07)

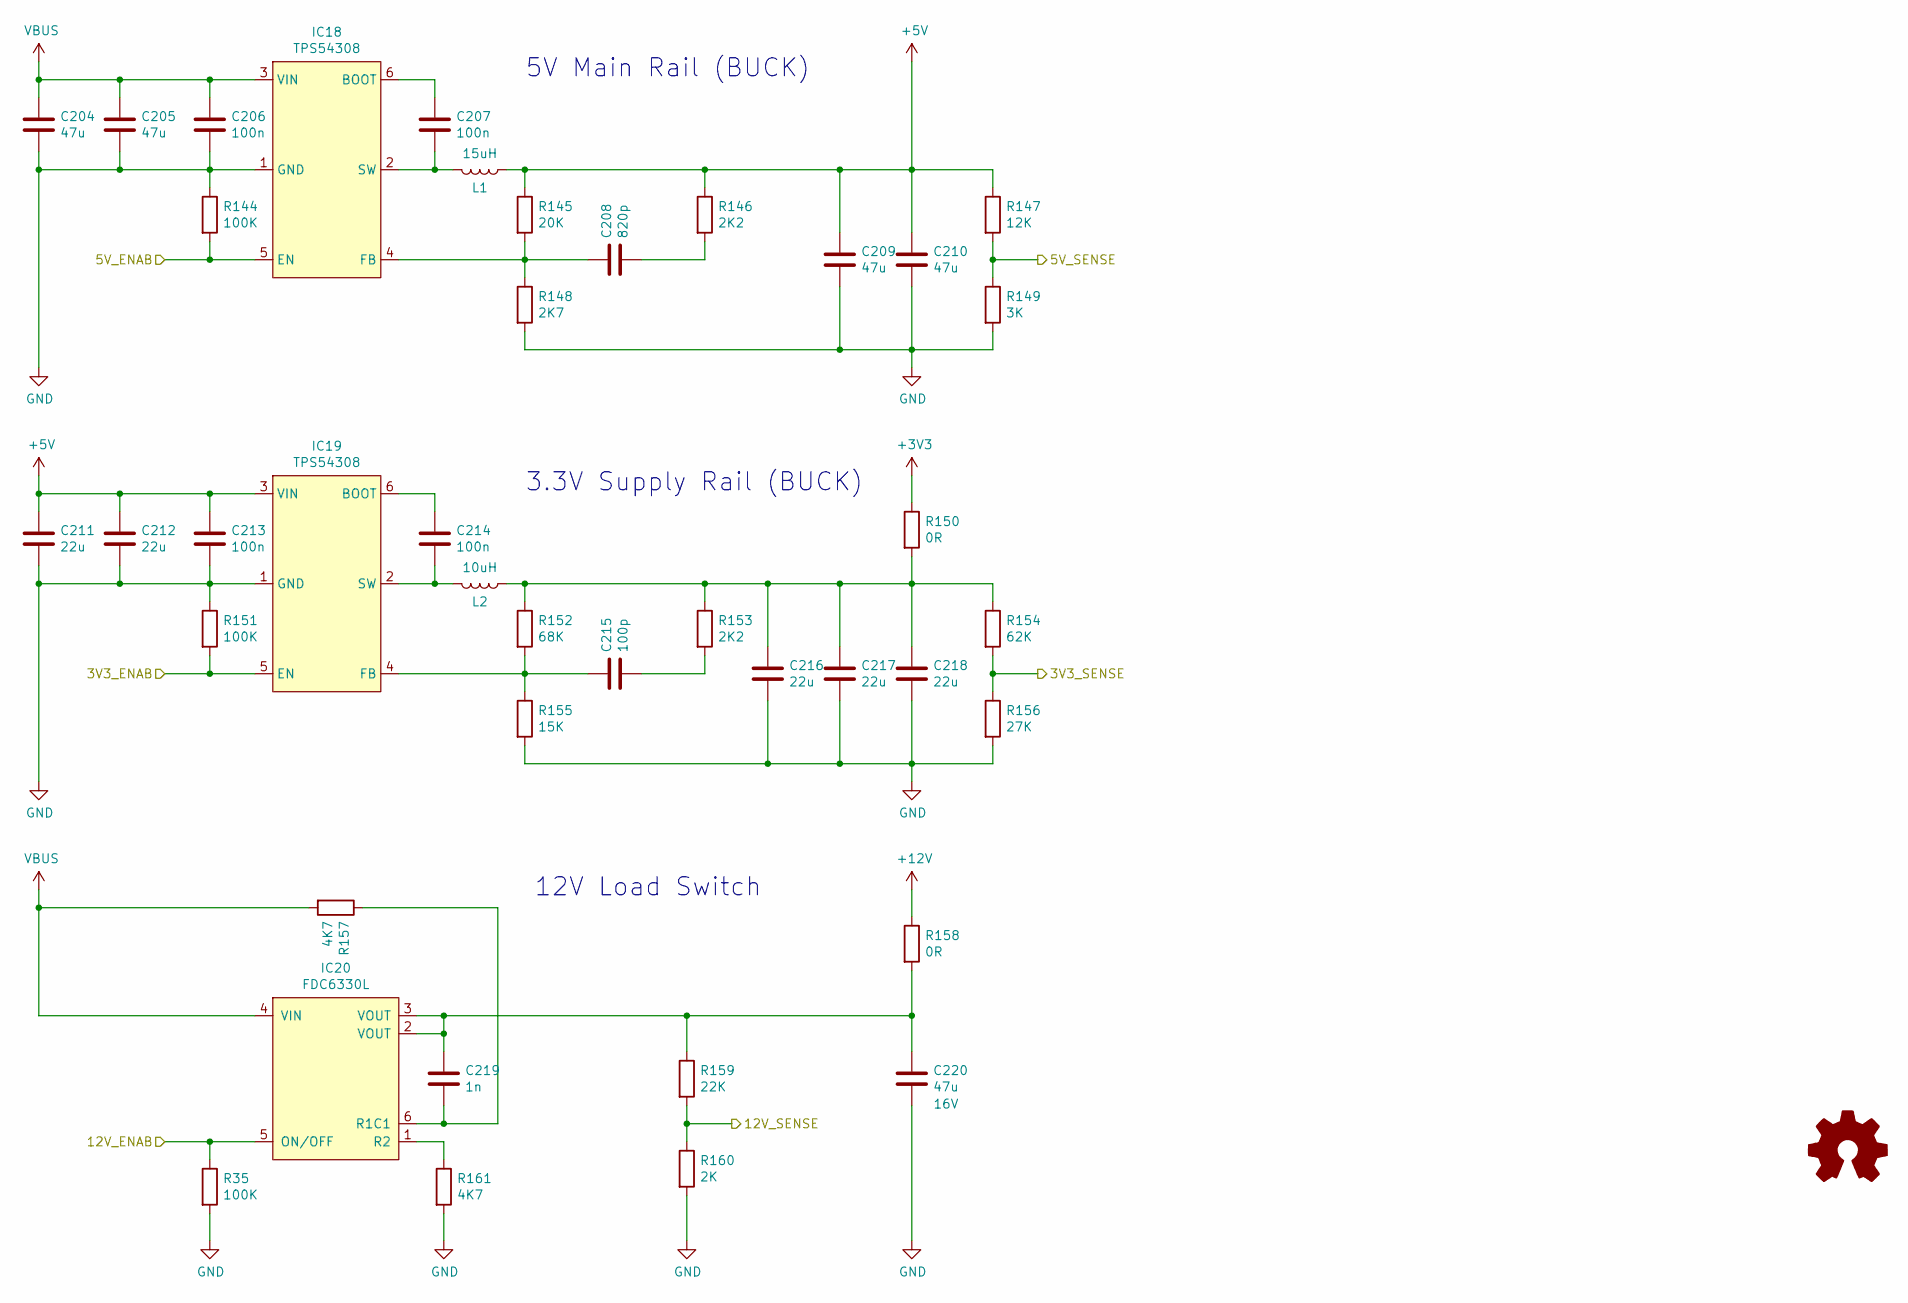
[picture p42: schematic PowerSupply1.sch]

Parts:
C204, C205, C209, C210: 47u; C_0805_2012Metric; MPN GRM21BR60J476ME15L
C206, C207, C213, C214: 100n; C_0603_1608Metric; MPN C0603C104M4RACTU
C208: 820p; C_0603_1608Metric; MPN C0603C821J5RACTU
C211, C212, C216, C217, C218: 22u; C_0805_2012Metric; MPN C0805C226M9PACTU
C215: 100p; C_0603_1608Metric; MPN C0603C101J5RACTU
C219: 1n; C_0603_1608Metric; MPN C0603C102K5RACTU
C220: 47u; C_1210_3225Metric; MPN GRM32EC81C476KE15L
IC18, IC19: TPS54308; SOT-23-6; MPN TPS54308DDCT
IC20: FDC6330L; MPN FDC6330L
L1: 15uH; L_Bourns_SRR1260; MPN SRR1260-150M
L2: 10uH; L_Bourns_SRR1260; MPN SRR1260-100M
R35, R144, R151: 100K; R_0603_1608Metric; MPN CRCW0603100KFKEA
R145: 20K; R_0603_1608Metric; MPN CRCW060320K0FKEA
R146, R153: 2K2; R_0603_1608Metric; MPN CRCW06032K20FKEA
R147: 12K; R_0603_1608Metric; MPN CRCW060312K0FKEA
R148: 2K7; R_0603_1608Metric; MPN CRCW06032K70FKEA
R149: 3K; R_0603_1608Metric; MPN CRCW06033K00FKEA
R150, R158: 0R; R_0805_2012Metric; MPN CRCW08050000Z0EA
R152: 68K; R_0603_1608Metric; MPN CRCW060368K0FKEA
R154: 62K; R_0603_1608Metric; MPN CRCW060362K0FKEA
R155: 15K; R_0603_1608Metric; MPN CRCW060315K0FKEA
R156: 27K; R_0603_1608Metric; MPN CRCW060327K0FKEA
R157, R161: 4K7; R_0603_1608Metric; MPN CRCW06034K70FKEA
R159: 22K; R_0603_1608Metric; MPN CRCW060322K0FKEA
R160: 2K; R_0603_1608Metric; MPN CRCW06032K00FKEA

Connections:
3V3_ENAB: IC19.5 (EN), R151.2
3V3_SENSE: R154.2, R156.1
5V_ENAB: IC18.5 (EN), R144.2
5V_SENSE: R147.2, R149.1
12V_ENAB: IC20.5 (ON/OFF), R35.1
12V_SENSE: R159.2, R160.1
+3V3: R150.1
+5V: C209.1, C210.1, C211.1, C212.1, C213.1, IC19.3 (VIN), L1.1, R145.1, R146.1, R147.1
+12V: R158.1
GND: C204.2, C205.2, C206.2, C209.2, C210.2, C211.2, C212.2, C213.2, C216.2, C217.2, C218.2, C220.2, IC18.1 (GND), IC19.1 (GND), R35.2, R144.1, R148.2, R149.2, R151.1, R155.2, R156.2, R160.2, R161.2
unnamed: C207.1, IC18.6 (BOOT)
unnamed: C207.2, IC18.2 (SW), L1.2
unnamed: C208.1, IC18.4 (FB), R145.2, R148.1
unnamed: C208.2, R146.2
unnamed: C214.1, IC19.6 (BOOT)
unnamed: C214.2, IC19.2 (SW), L2.2
unnamed: C215.1, IC19.4 (FB), R152.2, R155.1
unnamed: C215.2, R153.2
unnamed: C216.1, C217.1, C218.1, L2.1, R150.2, R152.1, R153.1, R154.1
unnamed: C219.1, C220.1, IC20.2 (VOUT), IC20.3 (VOUT), R158.2, R159.1
unnamed: C219.2, IC20.6 (R1C1), R157.1
unnamed: IC20.1 (R2), R161.1
VBUS: C204.1, C205.1, C206.1, IC18.3 (VIN), IC20.4 (VIN), R157.2

Notes on the sheet:
5V Main Rail (BUCK)
3.3V Supply Rail (BUCK)
12V Load Switch
