peterheinrich/ZHAW_DFF_RPI_Network_Lab_Board/ecad/PowerSupply2.sch

## KiCad design ecad/PowerSupply2.sch (2020-12-07)

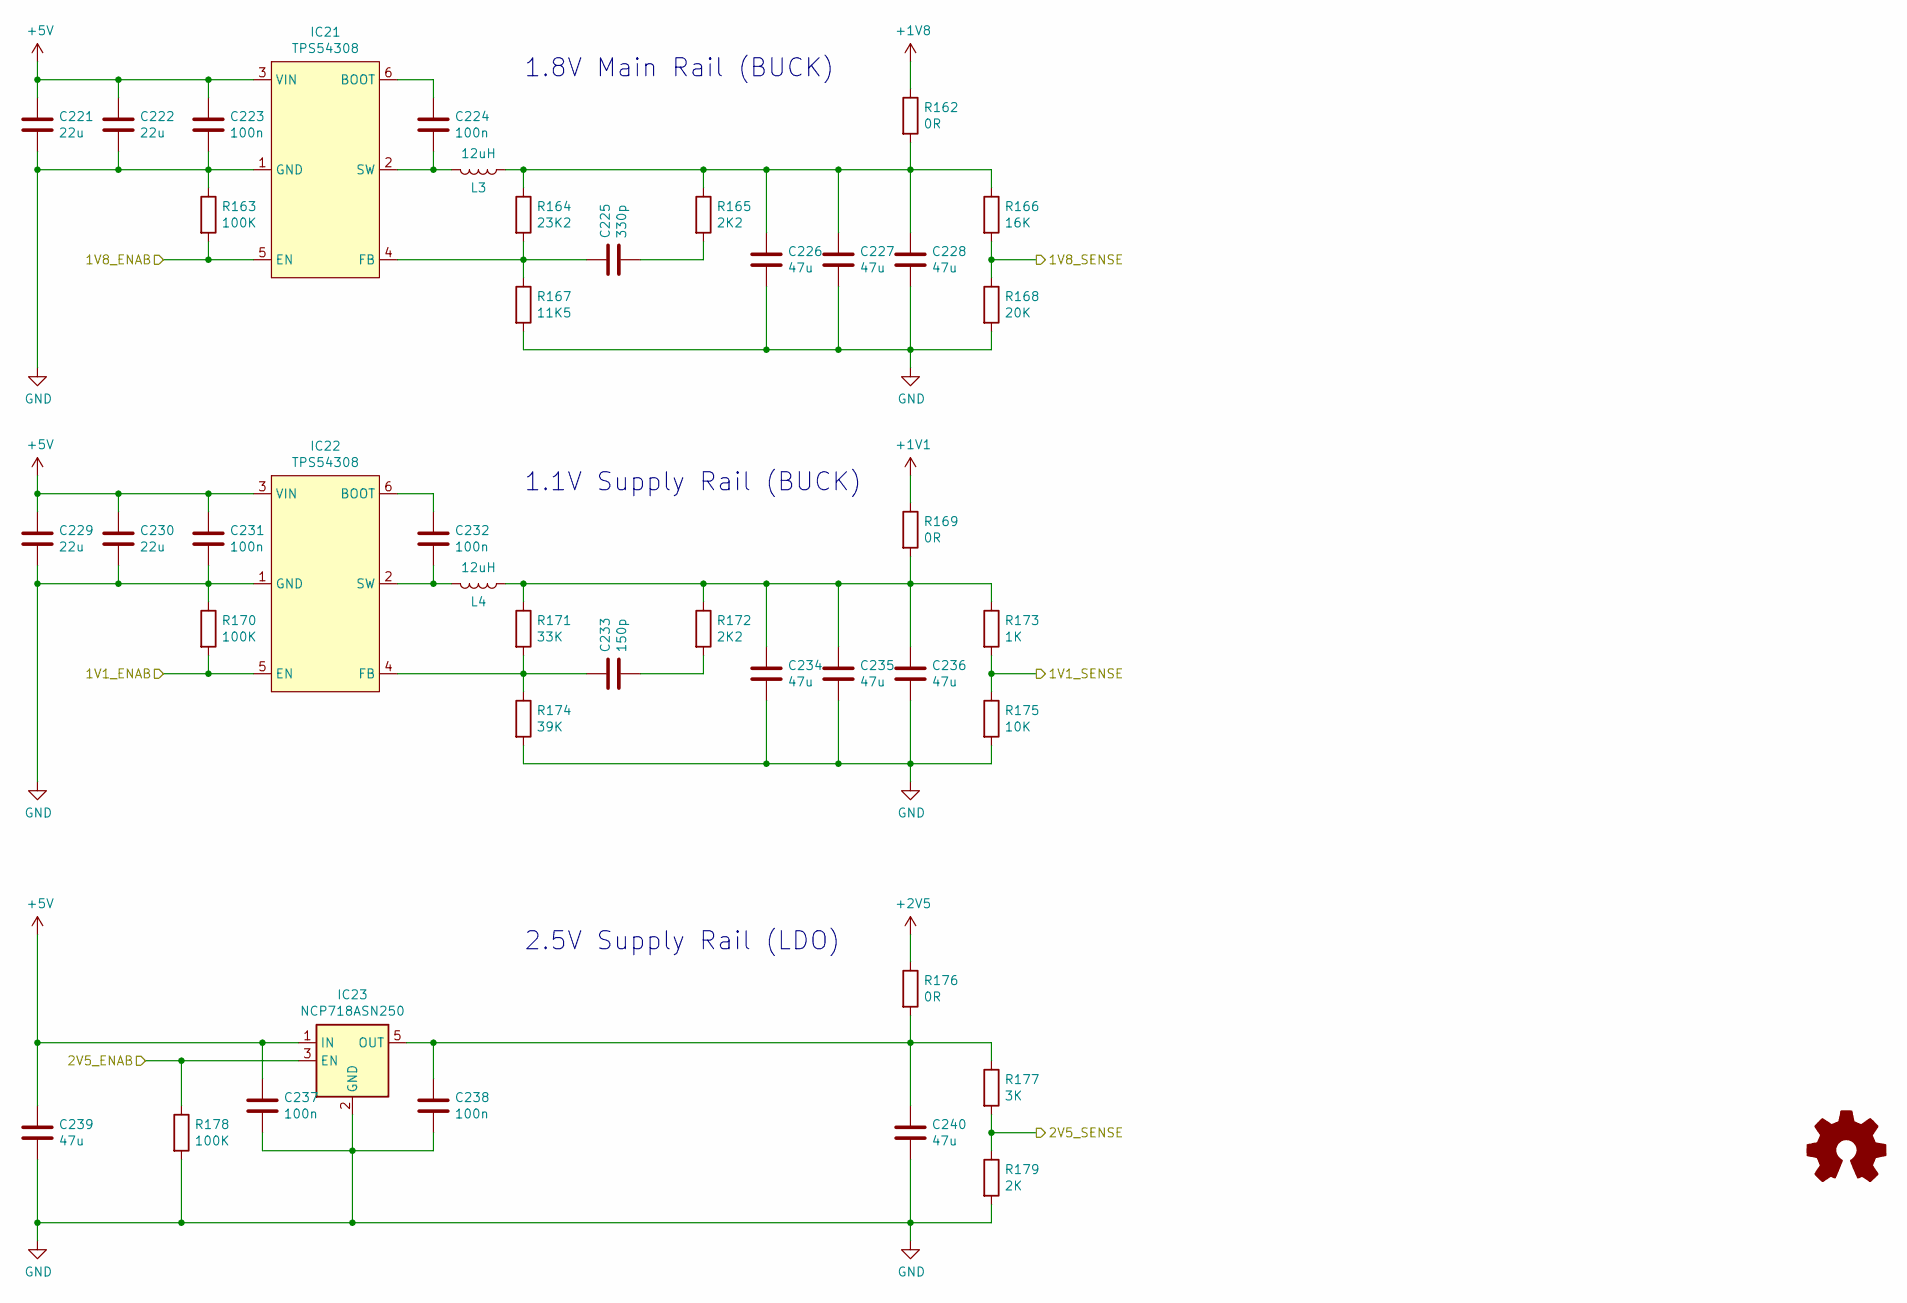
[picture p43: schematic PowerSupply2.sch]

Parts:
C221, C222, C229, C230: 22u; C_0805_2012Metric; MPN C0805C226M9PACTU
C223, C224, C231, C232, C237, C238: 100n; C_0603_1608Metric; MPN C0603C104M4RACTU
C225: 330p; C_0603_1608Metric; MPN C0603C331K5RACTU
C226, C227, C228, C234, C235, C236, C239, C240: 47u; C_0805_2012Metric; MPN GRM21BR60J476ME15L
C233: 150p; C_0603_1608Metric; MPN C0603C151J5GACTU
IC21, IC22: TPS54308; SOT-23-6; MPN TPS54308DDCT
IC23: NCP718ASN250; SOT-23-5; MPN NCP718ASN250T1G
L3, L4: 12uH; L_Bourns_SRR1260; MPN SRR1260-120M
R162, R169, R176: 0R; R_0805_2012Metric; MPN CRCW08050000Z0EA
R163, R170, R178: 100K; R_0603_1608Metric; MPN CRCW0603100KFKEA
R164: 23K2; R_0603_1608Metric; MPN CRCW060323K2FKEA
R165, R172: 2K2; R_0603_1608Metric; MPN CRCW06032K20FKEA
R166: 16K; R_0603_1608Metric; MPN CRCW060316K0FKEA
R167: 11K5; R_0603_1608Metric; MPN CRCW060311K5FKEA
R168: 20K; R_0603_1608Metric; MPN CRCW060320K0FKEA
R171: 33K; R_0603_1608Metric; MPN CRCW060333K0FKEA
R173: 1K; R_0603_1608Metric; MPN CRCW06031K00FKEA
R174: 39K; R_0603_1608Metric; MPN CRCW060339K0FKEA
R175: 10K; R_0603_1608Metric; MPN CRCW060310K0FKEA
R177: 3K; R_0603_1608Metric; MPN CRCW06033K00FKEA
R179: 2K; R_0603_1608Metric; MPN CRCW06032K00FKEA

Connections:
1V1_ENAB: IC22.5 (EN), R170.2
1V1_SENSE: R173.2, R175.1
1V8_ENAB: IC21.5 (EN), R163.2
1V8_SENSE: R166.2, R168.1
2V5_ENAB: IC23.3 (EN), R178.1
2V5_SENSE: R177.2, R179.1
+1V1: R169.1
+1V8: R162.1
+2V5: R176.1
+5V: C221.1, C222.1, C223.1, C229.1, C230.1, C231.1, C237.1, C239.1, IC21.3 (VIN), IC22.3 (VIN), IC23.1 (IN)
GND: C221.2, C222.2, C223.2, C226.2, C227.2, C228.2, C229.2, C230.2, C231.2, C234.2, C235.2, C236.2, C237.2, C238.2, C239.2, C240.2, IC21.1 (GND), IC22.1 (GND), IC23.2 (GND), R163.1, R167.2, R168.2, R170.1, R174.2, R175.2, R178.2, R179.2
unnamed: C224.1, IC21.6 (BOOT)
unnamed: C224.2, IC21.2 (SW), L3.2
unnamed: C225.1, IC21.4 (FB), R164.2, R167.1
unnamed: C225.2, R165.2
unnamed: C226.1, C227.1, C228.1, L3.1, R162.2, R164.1, R165.1, R166.1
unnamed: C232.1, IC22.6 (BOOT)
unnamed: C232.2, IC22.2 (SW), L4.2
unnamed: C233.1, IC22.4 (FB), R171.2, R174.1
unnamed: C233.2, R172.2
unnamed: C234.1, C235.1, C236.1, L4.1, R169.2, R171.1, R172.1, R173.1
unnamed: C238.1, C240.1, IC23.5 (OUT), R176.2, R177.1

Notes on the sheet:
2.5V Supply Rail (LDO)
1.8V Main Rail (BUCK)
1.1V Supply Rail (BUCK)
