peterheinrich/ZHAW_DFF_RPI_Network_Lab_Board/ecad/PowerSupply.sch

## KiCad design ecad/PowerSupply.sch (2020-12-07)

Schematic: PowerSupply.sch

Parts:
C1, C2, C4, C5, C15, C16, C18, C19: C
C3, C6, C7, C8, C17, C20, C21, C22: 100n; C_0603_1608Metric_Pad1.05x0.95mm_HandSolder; MPN CC0603KRX7R9BB104; LCSC_PART_NO C14663
C9, C10, C11, C12, C13, C14, C23, C24, C25, C26, C27, C28, C35: 47u; C_1206_3216Metric_Pad1.42x1.75mm_HandSolder; MPN CL31A476MPHNNNE; LCSC_PART_NO C96123
C29, C33: 100u
C30: 100n
C31, C32, C34: 1n
D1: 14V; MPN MMBZ5244BLT1G
F1: 2A
IC1, IC2, IC4, IC5: TPS54308; SOT-23-6
IC3: NCP718xSN120; SOT-23-5
IC6: LM2937IMP-3.3; SOT-223-3_TabPin2
IC7: FDC6330L
J1: DC_Supply; TerminalBlock_bornier-2_P5.08mm; MPN MC24366
L1, L2, L3, L4: L
L5: MSD1260-103MLB
Q1: Si2319CDS; SOT-23
R1, R2, R3, R4, R5, R6, R7, R8, R9, R10, R11, R12, R13, R15: R
R14, R16: 4K7

Notes on the sheet:
5V Main Rail (BUCK)
12V DC / 2A
3.3V Supply Rail (BUCK)
1.8V Supply Rail (BUCK)
1.1V Supply Rail (BUCK)
3.3V Standby (LIN)
2.5V Supply Rail (LDO)
12V Load Switch
