peterheinrich/ZHAW_DFF_RPI_Network_Lab_Board/ecad/RaspberryPi.sch

## KiCad design ecad/RaspberryPi.sch (2020-12-07)

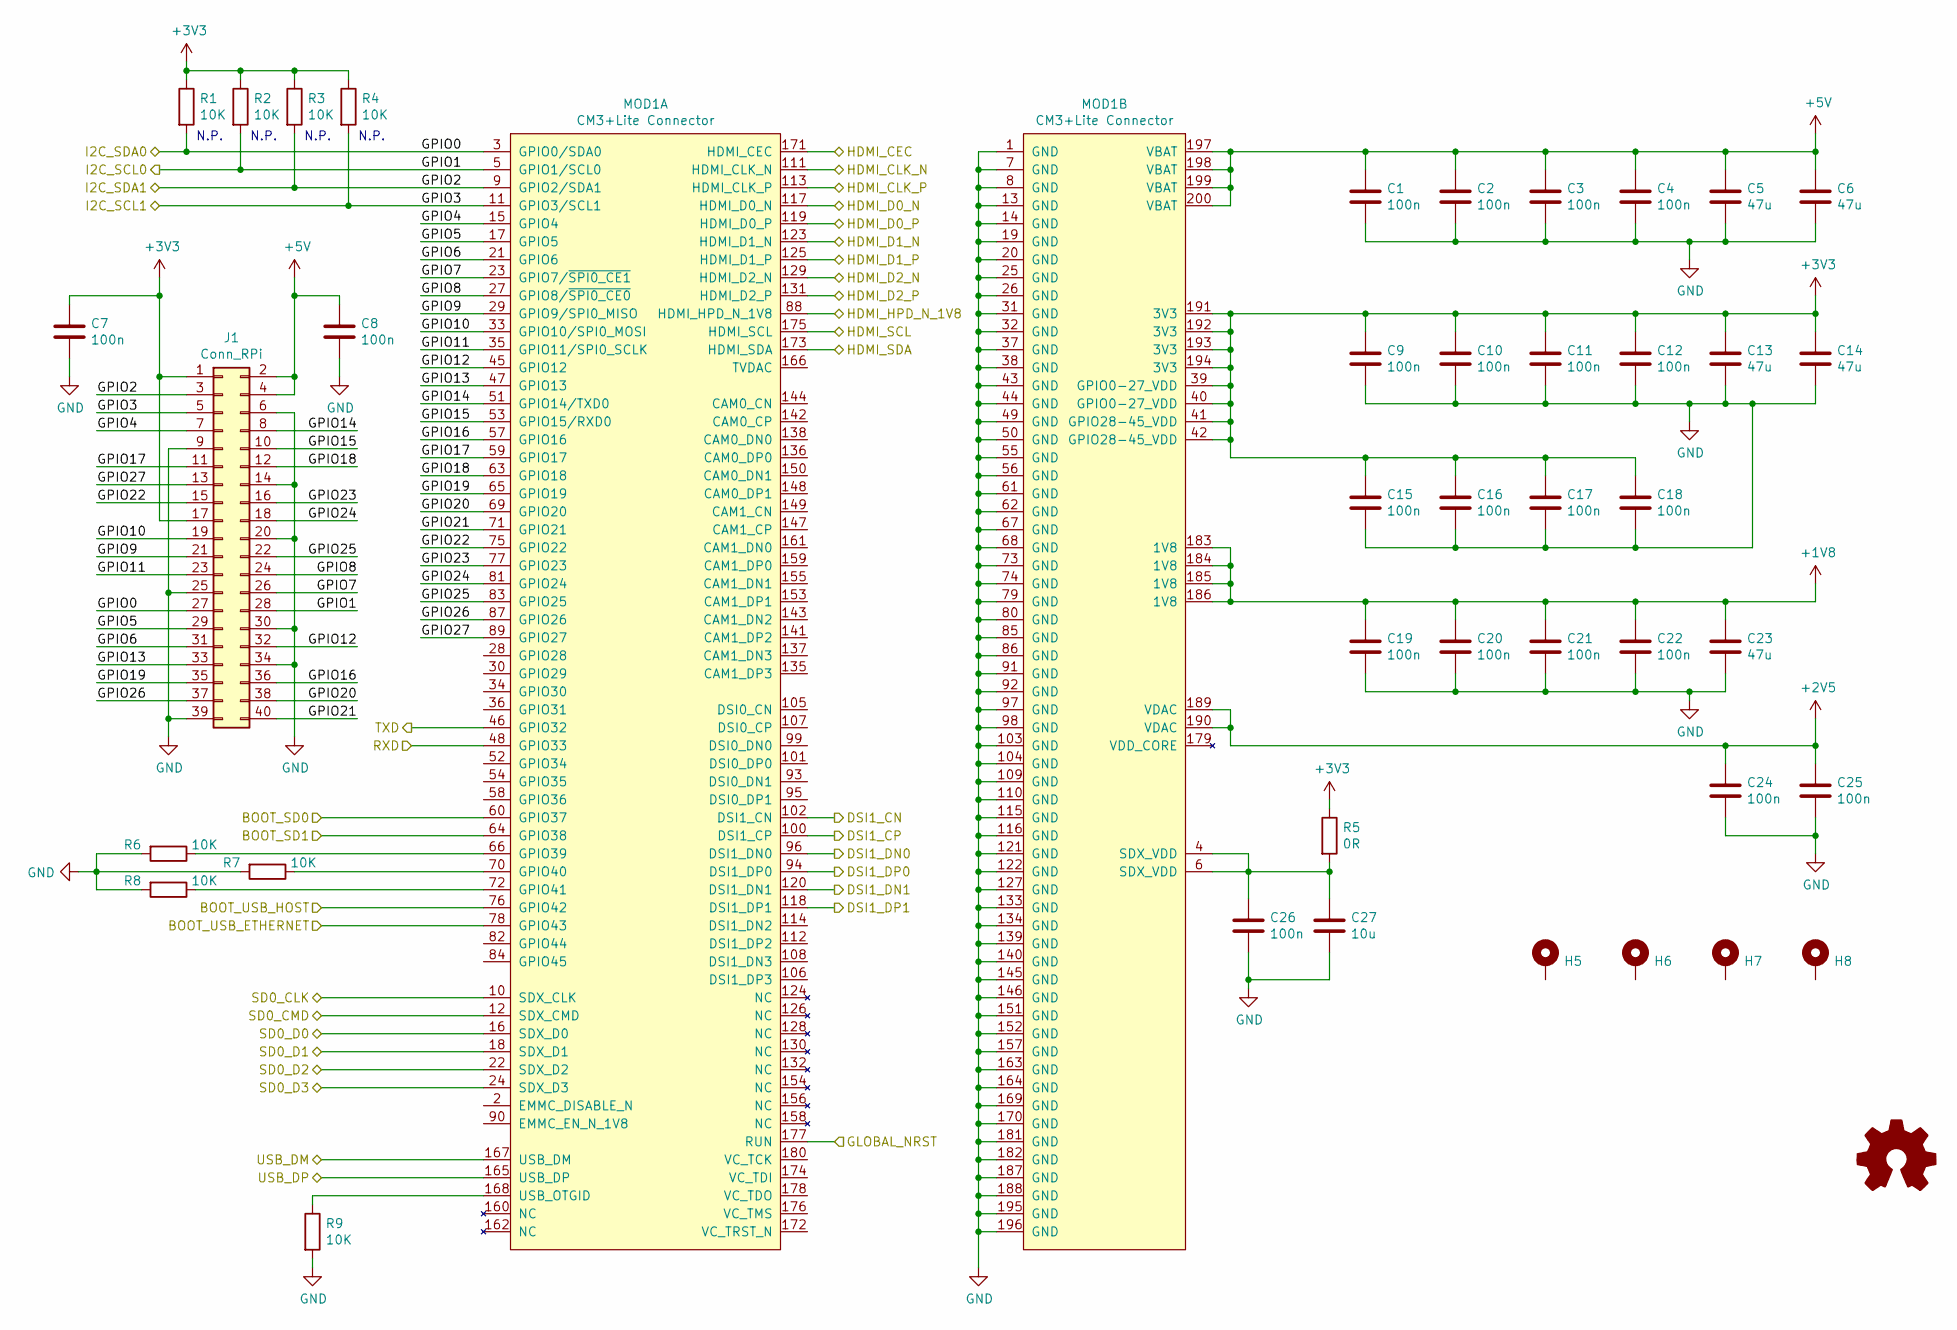
[picture p44: schematic RaspberryPi.sch]

Parts:
C1, C2, C3, C4, C7, C8, C9, C10, C11, C12, C15, C16, C17, C18, C19, C20, C21, C22, C24, C25, C26: 100n; C_0603_1608Metric; MPN C0603C104M4RACTU
C5, C6, C13, C14, C23: 47u; C_0805_2012Metric; MPN GRM21BR60J476ME15L
C27: 10u; C_0805_2012Metric; MPN C0805C106K8RACTU
H5, H6, H7, H8: MountingHole_Pad; MountingHole_2.7mm_M2.5_Pad_Via
J1: Conn_RPi; PinHeader_2x20_P2.54mm_Vertical; MPN 10-89-7402
MOD1: CM3+Lite Connector; 1612618-4; MPN 1612618-4
R1, R2, R3, R4, R6, R7, R8, R9: 10K; R_0603_1608Metric; MPN CRCW060310K0FKEA
R5: 0R; R_0603_1608Metric; MPN CRCW06030000Z0EA

Connections:
+1V8: C19.1, C20.1, C21.1, C22.1, C23.1, MOD1.183 (1V8), MOD1.184 (1V8), MOD1.185 (1V8), MOD1.186 (1V8)
+2V5: C24.1, C25.1, MOD1.189 (VDAC), MOD1.190 (VDAC)
+3V3: C7.1, C9.1, C10.1, C11.1, C12.1, C13.1, C14.1, C15.1, C16.1, C17.1, C18.1, J1.1, J1.17, MOD1.39 (GPIO0-27_VDD), MOD1.40 (GPIO0-27_VDD), MOD1.41 (GPIO28-45_VDD), MOD1.42 (GPIO28-45_VDD), MOD1.191 (3V3), MOD1.192 (3V3), MOD1.193 (3V3), MOD1.194 (3V3), R1.1, R2.1, R3.1, R4.1, R5.1
+5V: C1.1, C2.1, C3.1, C4.1, C5.1, C6.1, C8.1, J1.2, J1.4, MOD1.197 (VBAT), MOD1.198 (VBAT), MOD1.199 (VBAT), MOD1.200 (VBAT)
BOOT_SD0: MOD1.60 (GPIO37)
BOOT_SD1: MOD1.64 (GPIO38)
BOOT_USB_ETHERNET: MOD1.78 (GPIO43)
BOOT_USB_HOST: MOD1.76 (GPIO42)
DSI1_CN: MOD1.102 (DSI1_CN)
DSI1_CP: MOD1.100 (DSI1_CP)
DSI1_DN0: MOD1.96 (DSI1_DN0)
DSI1_DN1: MOD1.120 (DSI1_DN1)
DSI1_DP0: MOD1.94 (DSI1_DP0)
DSI1_DP1: MOD1.118 (DSI1_DP1)
GLOBAL_NRST: MOD1.177 (RUN)
GND: C1.2, C2.2, C3.2, C4.2, C5.2, C6.2, C7.2, C8.2, C9.2, C10.2, C11.2, C12.2, C13.2, C14.2, C15.2, C16.2, C17.2, C18.2, C19.2, C20.2, C21.2, C22.2, C23.2, C24.2, C25.2, C26.2, C27.2, J1.6, J1.9, J1.14, J1.20, J1.25, J1.30, J1.34, J1.39, MOD1.1 (GND), MOD1.7 (GND), MOD1.8 (GND), MOD1.13 (GND), MOD1.14 (GND), MOD1.19 (GND), MOD1.20 (GND), MOD1.25 (GND), MOD1.26 (GND), MOD1.31 (GND), MOD1.32 (GND), MOD1.37 (GND), MOD1.38 (GND), MOD1.43 (GND), MOD1.44 (GND), MOD1.49 (GND), MOD1.50 (GND), MOD1.55 (GND), MOD1.56 (GND), MOD1.61 (GND), MOD1.62 (GND), MOD1.67 (GND), MOD1.68 (GND), MOD1.73 (GND), MOD1.74 (GND), MOD1.79 (GND), MOD1.80 (GND), MOD1.85 (GND), MOD1.86 (GND), MOD1.91 (GND), MOD1.92 (GND), MOD1.97 (GND), MOD1.98 (GND), MOD1.103 (GND), MOD1.104 (GND), MOD1.109 (GND), MOD1.110 (GND), MOD1.115 (GND), MOD1.116 (GND), MOD1.121 (GND), MOD1.122 (GND), MOD1.127 (GND), MOD1.133 (GND), MOD1.134 (GND), MOD1.139 (GND), MOD1.140 (GND), MOD1.145 (GND), MOD1.146 (GND), MOD1.151 (GND), MOD1.152 (GND), MOD1.157 (GND), MOD1.163 (GND), MOD1.164 (GND), MOD1.169 (GND), MOD1.170 (GND), MOD1.181 (GND), MOD1.182 (GND), MOD1.187 (GND), MOD1.188 (GND), MOD1.195 (GND), MOD1.196 (GND), R6.2, R7.2, R8.2, R9.2
GPIO0: J1.27, MOD1.3 (GPIO0/SDA0), R1.2
GPIO1: J1.28, MOD1.5 (GPIO1/SCL0), R2.2
GPIO2: J1.3, MOD1.9 (GPIO2/SDA1), R3.2
GPIO3: J1.5, MOD1.11 (GPIO3/SCL1), R4.2
GPIO4: J1.7, MOD1.15 (GPIO4)
GPIO5: J1.29, MOD1.17 (GPIO5)
GPIO6: J1.31, MOD1.21 (GPIO6)
GPIO7: J1.26, MOD1.23 (GPIO7/~SPI0_CE1)
GPIO8: J1.24, MOD1.27 (GPIO8/~SPI0_CE0)
GPIO9: J1.21, MOD1.29 (GPIO9/SPI0_MISO)
GPIO10: J1.19, MOD1.33 (GPIO10/SPI0_MOSI)
GPIO11: J1.23, MOD1.35 (GPIO11/SPI0_SCLK)
GPIO12: J1.32, MOD1.45 (GPIO12)
GPIO13: J1.33, MOD1.47 (GPIO13)
GPIO14: J1.8, MOD1.51 (GPIO14/TXD0)
GPIO15: J1.10, MOD1.53 (GPIO15/RXD0)
GPIO16: J1.36, MOD1.57 (GPIO16)
GPIO17: J1.11, MOD1.59 (GPIO17)
GPIO18: J1.12, MOD1.63 (GPIO18)
GPIO19: J1.35, MOD1.65 (GPIO19)
GPIO20: J1.38, MOD1.69 (GPIO20)
GPIO21: J1.40, MOD1.71 (GPIO21)
GPIO22: J1.15, MOD1.75 (GPIO22)
GPIO23: J1.16, MOD1.77 (GPIO23)
GPIO24: J1.18, MOD1.81 (GPIO24)
GPIO25: J1.22, MOD1.83 (GPIO25)
GPIO26: J1.37, MOD1.87 (GPIO26)
GPIO27: J1.13, MOD1.89 (GPIO27)
HDMI_CEC: MOD1.171 (HDMI_CEC)
HDMI_CLK_N: MOD1.111 (HDMI_CLK_N)
HDMI_CLK_P: MOD1.113 (HDMI_CLK_P)
HDMI_D0_N: MOD1.117 (HDMI_D0_N)
HDMI_D0_P: MOD1.119 (HDMI_D0_P)
HDMI_D1_N: MOD1.123 (HDMI_D1_N)
HDMI_D1_P: MOD1.125 (HDMI_D1_P)
HDMI_D2_N: MOD1.129 (HDMI_D2_N)
HDMI_D2_P: MOD1.131 (HDMI_D2_P)
HDMI_HPD_N_1V8: MOD1.88 (HDMI_HPD_N_1V8)
HDMI_SCL: MOD1.175 (HDMI_SCL)
HDMI_SDA: MOD1.173 (HDMI_SDA)
unnamed: C26.1, C27.1, MOD1.4 (SDX_VDD), MOD1.6 (SDX_VDD), R5.2
unnamed: MOD1.66 (GPIO39), R6.1
unnamed: MOD1.70 (GPIO40), R7.1
unnamed: MOD1.72 (GPIO41), R8.1
unnamed: MOD1.168 (USB_OTGID), R9.1
RXD: MOD1.48 (GPIO33)
SD0_CLK: MOD1.10 (SDX_CLK)
SD0_CMD: MOD1.12 (SDX_CMD)
SD0_D0: MOD1.16 (SDX_D0)
SD0_D1: MOD1.18 (SDX_D1)
SD0_D2: MOD1.22 (SDX_D2)
SD0_D3: MOD1.24 (SDX_D3)
TXD: MOD1.46 (GPIO32)
USB_DM: MOD1.167 (USB_DM)
USB_DP: MOD1.165 (USB_DP)

Notes on the sheet:
N.P.
