peterheinrich/ZHAW_DFF_RPI_Network_Lab_Board/ecad/RpiSecLab.sch

## KiCad design ecad/RpiSecLab.sch (2020-12-07)

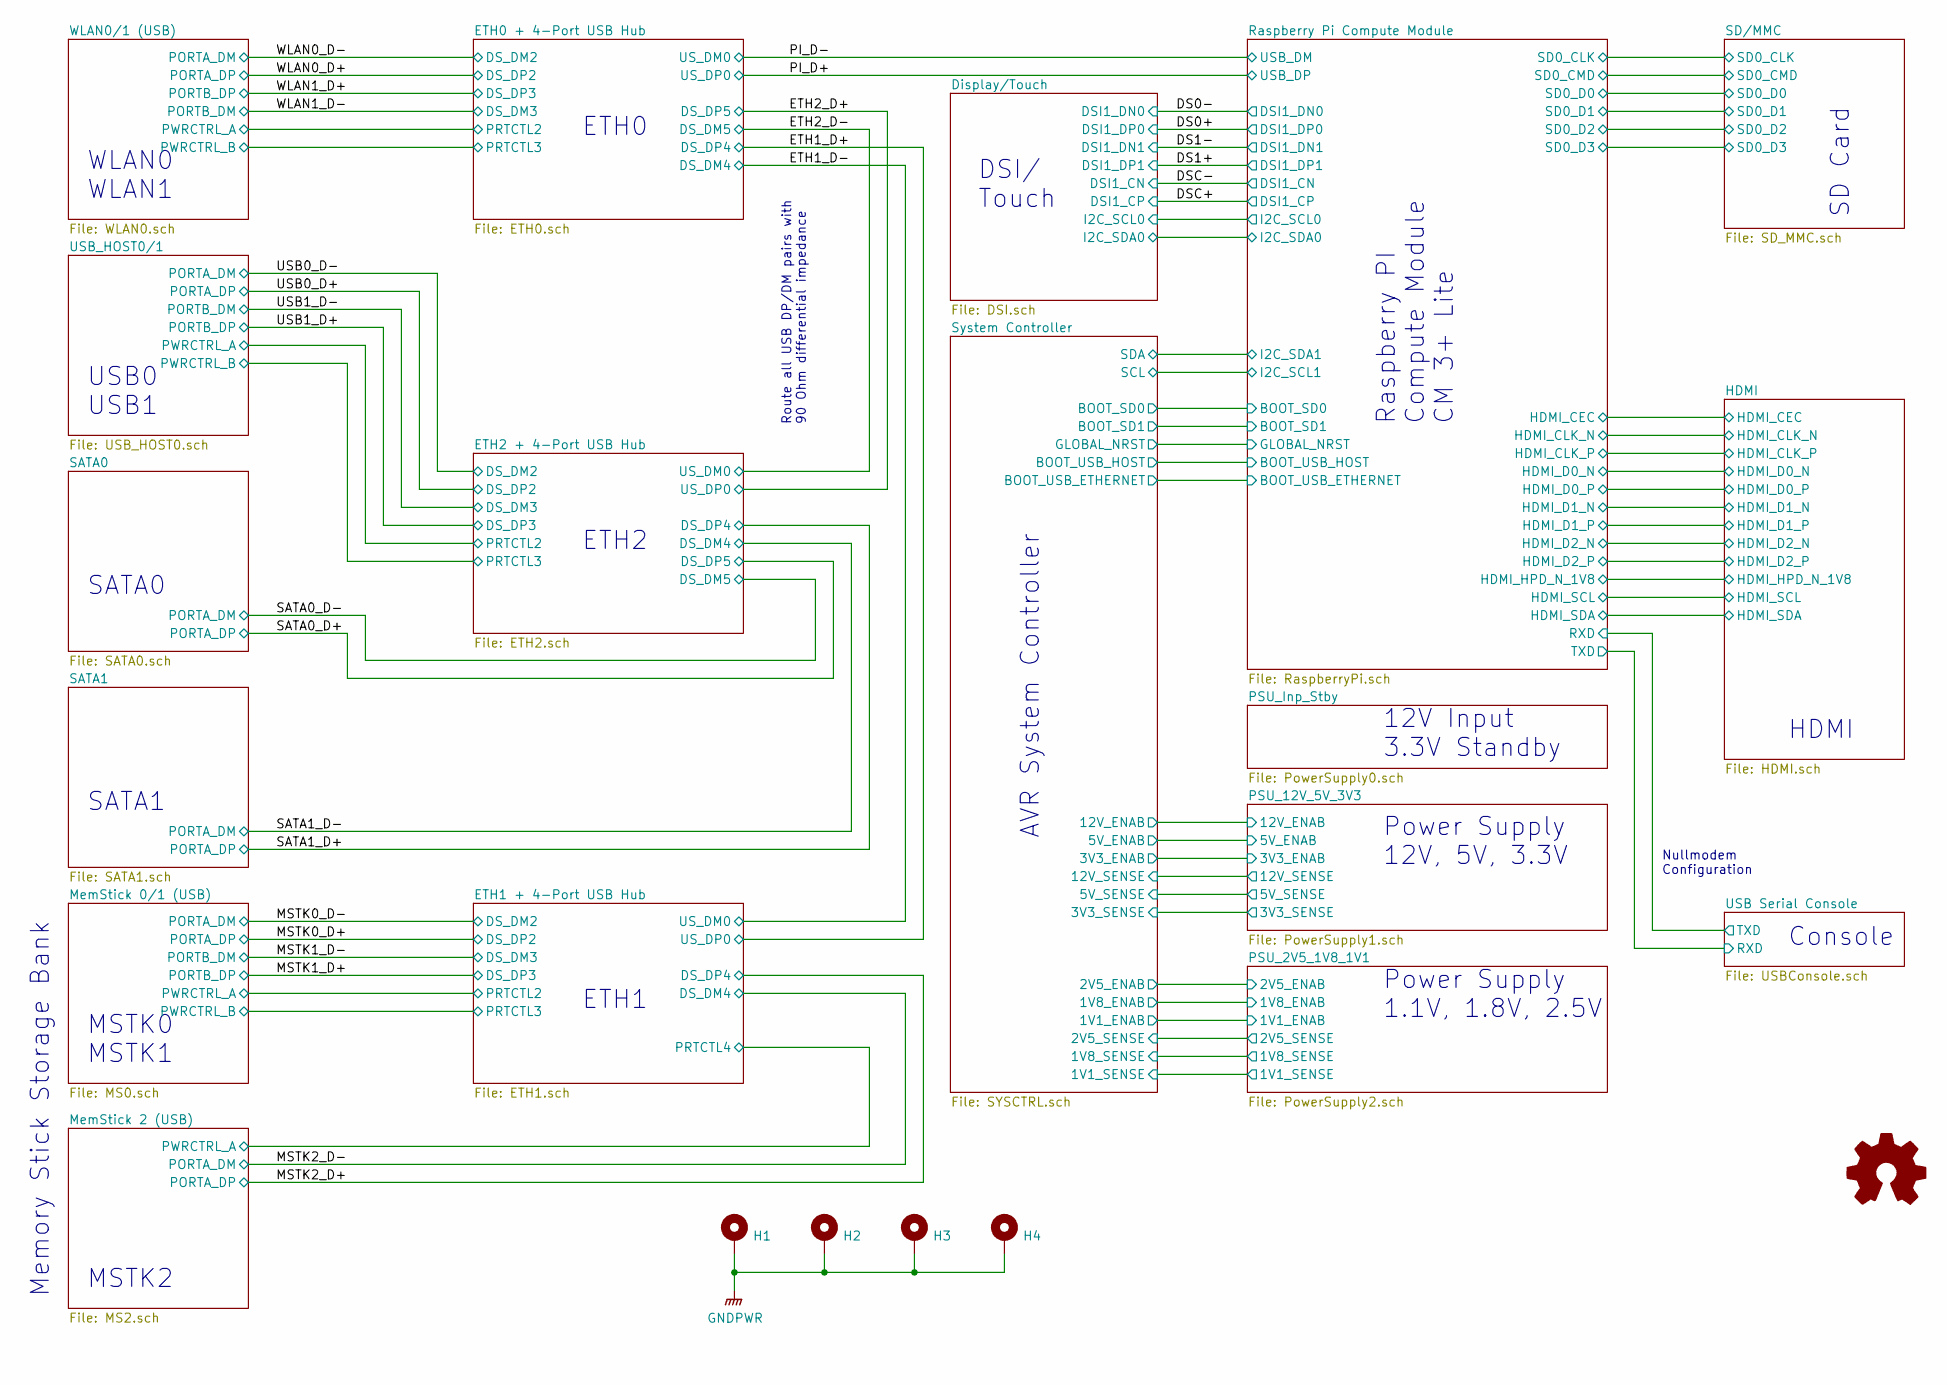
[picture p45: schematic RpiSecLab.sch]

Parts:
H1, H2, H3, H4: MountingHole_Pad; MountingHole_2.7mm_M2.5_Pad_Via

Connections:
GNDPWR: H1.1, H2.1, H3.1, H4.1

Notes on the sheet:
Raspberry PI Compute Module CM 3+ Lite
Nullmodem Configuration
WLAN0 WLAN1
MSTK2
ETH0
Console
HDMI
SD Card
DSI/ Touch
Memory Stick Storage Bank
Power Supply 1.1V, 1.8V, 2.5V
Power Supply 12V, 5V, 3.3V
12V Input 3.3V Standby
AVR System Controller
ETH2
SATA0
USB0 USB1
Route all USB DP/DM pairs with 90 Ohm differential impedance
ETH1
MSTK0 MSTK1
SATA1
