peterheinrich/ZHAW_DFF_RPI_Network_Lab_Board/ecad/SATA0.sch

## KiCad design ecad/SATA0.sch (2020-12-07)

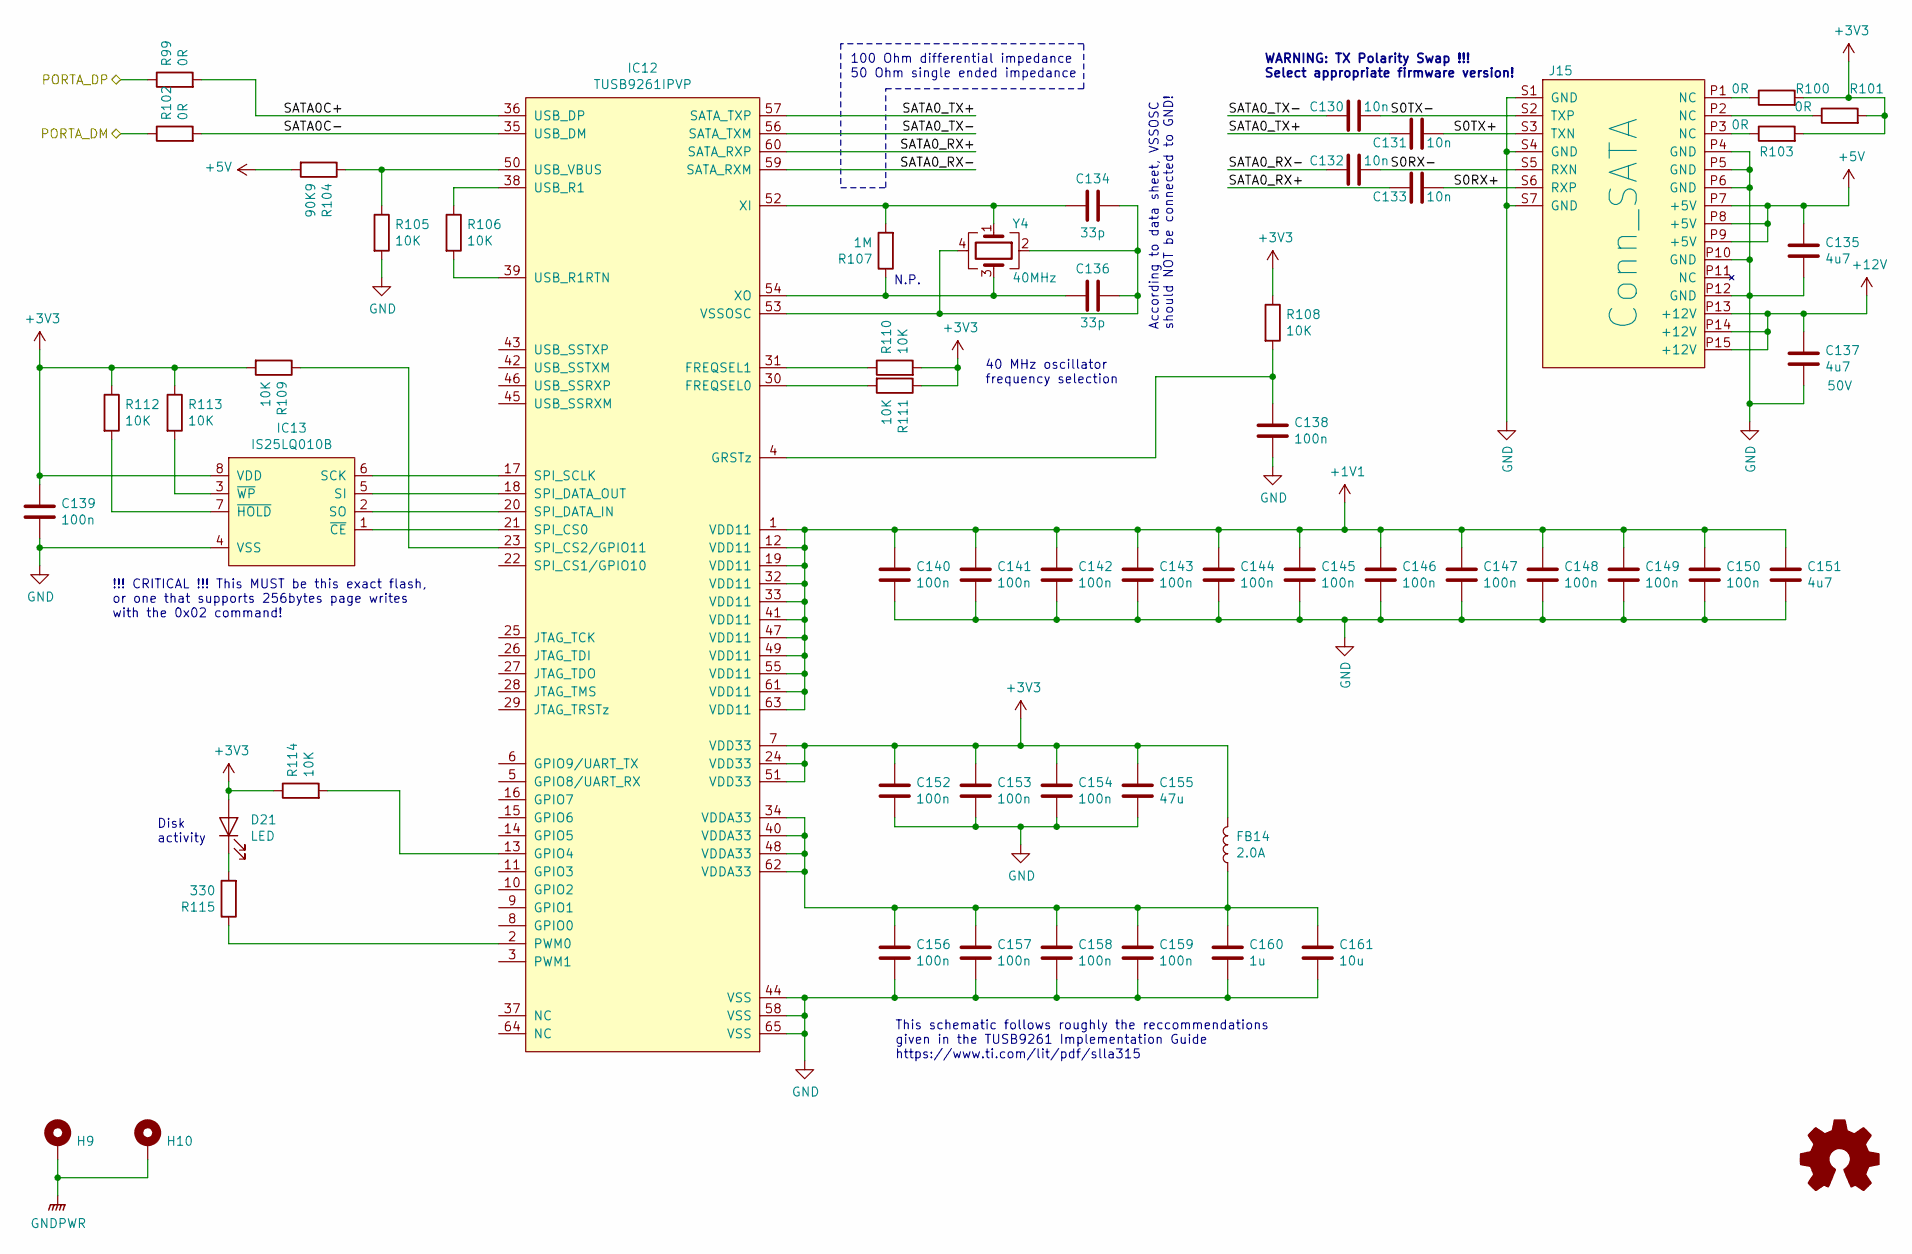
[picture p46: schematic SATA0.sch]

Parts:
C130, C131, C132, C133: 10n; C_0603_1608Metric; MPN C0603C103K1RACTU
C134, C136: 33p; C_0603_1608Metric; MPN C0603C330J5GACTU
C135, C137, C151: 4u7; C_0805_2012Metric; MPN GRM21BR61H475KE51L
C138, C139, C140, C141, C142, C143, C144, C145, C146, C147, C148, C149, C150, C152, C153, C154, C156, C157, C158, C159: 100n; C_0603_1608Metric; MPN C0603C104M4RACTU
C155: 47u; C_0805_2012Metric; MPN GRM21BR60J476ME15L
C160: 1u; C_0805_2012Metric; MPN C0805C105K3PACTU
C161: 10u; C_0805_2012Metric; MPN C0805C106K8RACTU
D21: LED; LED_0805_2012Metric_Pad1.15x1.40mm_HandSolder; MPN KP-2012LSGC
FB14: 2.0A; L_0603_1608Metric_Pad1.05x0.95mm_HandSolder; MPN BLM18PG121SN1D
H9, H10: MountingHole_Pad; MountingHole_2.7mm_M2.5_Pad_Via
IC12: TUSB9261IPVP; PQFP-64_7x7mm_P0.4mm; MPN TUSB9261IPVP
IC13: IS25LQ010B; SOIC-8_3.9x4.9mm_P1.27mm; MPN IS25LQ010B-JNLE
J15: Conn_SATA; 87678-1001; MPN 87678-1001
R99, R102: 0R; R_0603_1608Metric; MPN CRCW06030000Z0EA
R100, R101, R103: 0R; R_0805_2012Metric; MPN CRCW08050000Z0EA
R104: 90K9; R_0603_1608Metric; MPN CRCW060390K9FKEA
R105, R106, R108, R109, R110, R111, R112, R113, R114: 10K; R_0603_1608Metric; MPN CRCW060310K0FKEA
R107: 1M; R_0603_1608Metric; MPN CRCW06031M00FKEA
R115: 330; R_0603_1608Metric; MPN CRCW0603330RFKEA
Y4: 40MHz; Crystal_SMD_Abracon_ABM8G-4Pin_3.2x2.5mm; MPN ABM8-40.000MHZ-10-D1G-T

Connections:
+1V1: C140.1, C141.1, C142.1, C143.1, C144.1, C145.1, C146.1, C147.1, C148.1, C149.1, C150.1, C151.1, IC12.1 (VDD11), IC12.12 (VDD11), IC12.19 (VDD11), IC12.32 (VDD11), IC12.33 (VDD11), IC12.41 (VDD11), IC12.47 (VDD11), IC12.49 (VDD11), IC12.55 (VDD11), IC12.61 (VDD11), IC12.63 (VDD11)
+3V3: C139.1, C152.1, C153.1, C154.1, C155.1, D21.2 (A), FB14.2, IC12.7 (VDD33), IC12.24 (VDD33), IC12.51 (VDD33), IC13.8 (VDD), R100.2, R101.2, R103.2, R108.1, R109.2, R110.2, R111.1, R112.1, R113.1, R114.1
+5V: C135.1, J15.P7 (+5V), J15.P8 (+5V), J15.P9 (+5V), R104.2
+12V: C137.1, J15.P13 (+12V), J15.P14 (+12V), J15.P15 (+12V)
GND: C135.2, C137.2, C138.2, C139.2, C140.2, C141.2, C142.2, C143.2, C144.2, C145.2, C146.2, C147.2, C148.2, C149.2, C150.2, C151.2, C152.2, C153.2, C154.2, C155.2, C156.2, C157.2, C158.2, C159.2, C160.2, C161.2, IC12.44 (VSS), IC12.58 (VSS), IC12.65 (VSS), IC13.4 (VSS), J15.P4 (GND), J15.P5 (GND), J15.P6 (GND), J15.P10 (GND), J15.P12 (GND), J15.S1 (GND), J15.S4 (GND), J15.S7 (GND), R105.2
GNDPWR: H9.1, H10.1
unnamed: C134.1, C136.1, IC12.53 (VSSOSC), Y4.2, Y4.4
unnamed: C134.2, IC12.52 (XI), R107.2, Y4.1
unnamed: C136.2, IC12.54 (XO), R107.1, Y4.3
unnamed: C138.1, IC12.4 (GRSTz), R108.2
unnamed: C156.1, C157.1, C158.1, C159.1, C160.1, C161.1, FB14.1, IC12.34 (VDDA33), IC12.40 (VDDA33), IC12.48 (VDDA33), IC12.62 (VDDA33)
unnamed: D21.1 (K), R115.2
unnamed: IC12.2 (PWM0), R115.1
unnamed: IC12.13 (GPIO4), R114.2
unnamed: IC12.17 (SPI_SCLK), IC13.6 (SCK)
unnamed: IC12.18 (SPI_DATA_OUT), IC13.5 (SI)
unnamed: IC12.20 (SPI_DATA_IN), IC13.2 (SO)
unnamed: IC12.21 (SPI_CS0), IC13.1 (~CE)
unnamed: IC12.23 (SPI_CS2/GPIO11), R109.1
unnamed: IC12.30 (FREQSEL0), R111.2
unnamed: IC12.31 (FREQSEL1), R110.1
unnamed: IC12.38 (USB_R1), R106.1
unnamed: IC12.39 (USB_R1RTN), R106.2
unnamed: IC12.50 (USB_VBUS), R104.1, R105.1
unnamed: IC13.3 (~WP), R113.2
unnamed: IC13.7 (~HOLD), R112.2
unnamed: J15.P1 (NC), R100.1
unnamed: J15.P2 (NC), R101.1
unnamed: J15.P3 (NC), R103.1
PORTA_DM: R102.1
PORTA_DP: R99.1
S0RX+: C133.1, J15.S6 (RXP)
S0RX-: C132.2, J15.S5 (RXN)
S0TX+: C131.1, J15.S3 (TXN)
S0TX-: C130.2, J15.S2 (TXP)
SATA0C+: IC12.36 (USB_DP), R99.2
SATA0C-: IC12.35 (USB_DM), R102.2
SATA0_RX+: C133.2, IC12.60 (SATA_RXP)
SATA0_RX-: C132.1, IC12.59 (SATA_RXM)
SATA0_TX+: C131.2, IC12.57 (SATA_TXP)
SATA0_TX-: C130.1, IC12.56 (SATA_TXM)

Notes on the sheet:
N.P.
40 MHz oscillator frequency selection
100 Ohm differential impedance 50 Ohm single ended impedance
Disk activity
WARNING: TX Polarity Swap !!! Select appropriate firmware version!
According to data sheet, VSSOSC should NOT be connected to GND!
!!! CRITICAL !!! This MUST be this exact flash, or one that supports 256bytes page writes with the 0x02 command!
This schematic follows roughly the reccommendations given in the TUSB9261 Implementation Guide https://www.ti.com/lit/pdf/slla315
