peterheinrich/ZHAW_DFF_RPI_Network_Lab_Board/ecad/SATA1.sch

## KiCad design ecad/SATA1.sch (2020-12-07)

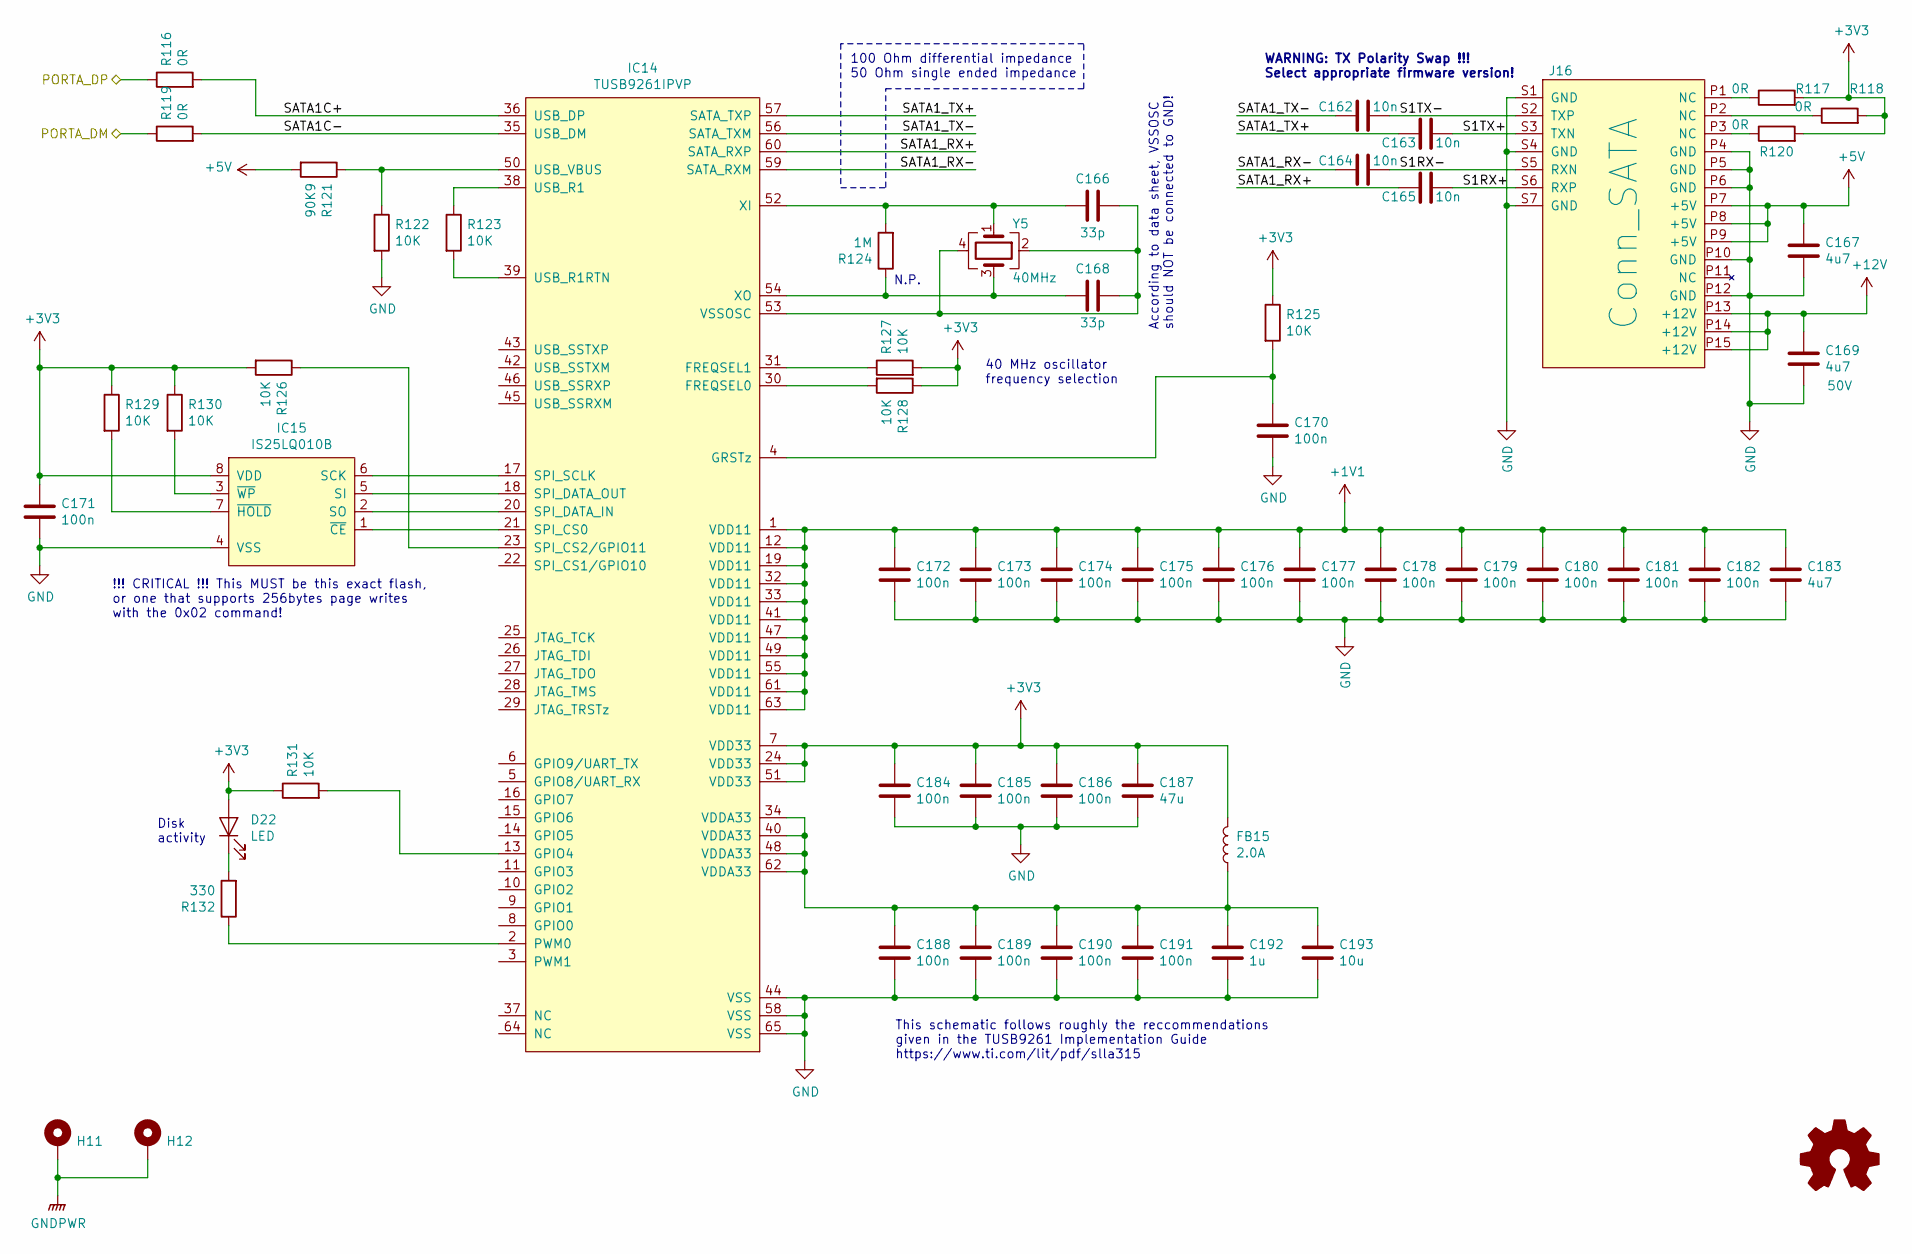
[picture p47: schematic SATA1.sch]

Parts:
C162, C163, C164, C165: 10n; C_0603_1608Metric; MPN C0603C103K1RACTU
C166, C168: 33p; C_0603_1608Metric; MPN C0603C330J5GACTU
C167, C169, C183: 4u7; C_0805_2012Metric; MPN GRM21BR61H475KE51L
C170, C171, C172, C173, C174, C175, C176, C177, C178, C179, C180, C181, C182, C184, C185, C186, C188, C189, C190, C191: 100n; C_0603_1608Metric; MPN C0603C104M4RACTU
C187: 47u; C_0805_2012Metric; MPN GRM21BR60J476ME15L
C192: 1u; C_0805_2012Metric; MPN C0805C105K3PACTU
C193: 10u; C_0805_2012Metric; MPN C0805C106K8RACTU
D22: LED; LED_0805_2012Metric_Pad1.15x1.40mm_HandSolder; MPN KP-2012LSGC
FB15: 2.0A; L_0603_1608Metric_Pad1.05x0.95mm_HandSolder; MPN BLM18PG121SN1D
H11, H12: MountingHole_Pad; MountingHole_2.7mm_M2.5_Pad_Via
IC14: TUSB9261IPVP; PQFP-64_7x7mm_P0.4mm; MPN TUSB9261IPVP
IC15: IS25LQ010B; SOIC-8_3.9x4.9mm_P1.27mm; MPN IS25LQ010B-JNLE
J16: Conn_SATA; 87678-1001; MPN 87678-1001
R116, R119: 0R; R_0603_1608Metric; MPN CRCW06030000Z0EA
R117, R118, R120: 0R; R_0805_2012Metric; MPN CRCW08050000Z0EA
R121: 90K9; R_0603_1608Metric; MPN CRCW060390K9FKEA
R122, R123, R125, R126, R127, R128, R129, R130, R131: 10K; R_0603_1608Metric; MPN CRCW060310K0FKEA
R124: 1M; R_0603_1608Metric; MPN CRCW06031M00FKEA
R132: 330; R_0603_1608Metric; MPN CRCW0603330RFKEA
Y5: 40MHz; Crystal_SMD_Abracon_ABM8G-4Pin_3.2x2.5mm; MPN ABM8-40.000MHZ-10-D1G-T

Connections:
+1V1: C172.1, C173.1, C174.1, C175.1, C176.1, C177.1, C178.1, C179.1, C180.1, C181.1, C182.1, C183.1, IC14.1 (VDD11), IC14.12 (VDD11), IC14.19 (VDD11), IC14.32 (VDD11), IC14.33 (VDD11), IC14.41 (VDD11), IC14.47 (VDD11), IC14.49 (VDD11), IC14.55 (VDD11), IC14.61 (VDD11), IC14.63 (VDD11)
+3V3: C171.1, C184.1, C185.1, C186.1, C187.1, D22.2 (A), FB15.2, IC14.7 (VDD33), IC14.24 (VDD33), IC14.51 (VDD33), IC15.8 (VDD), R117.2, R118.2, R120.2, R125.1, R126.2, R127.2, R128.1, R129.1, R130.1, R131.1
+5V: C167.1, J16.P7 (+5V), J16.P8 (+5V), J16.P9 (+5V), R121.2
+12V: C169.1, J16.P13 (+12V), J16.P14 (+12V), J16.P15 (+12V)
GND: C167.2, C169.2, C170.2, C171.2, C172.2, C173.2, C174.2, C175.2, C176.2, C177.2, C178.2, C179.2, C180.2, C181.2, C182.2, C183.2, C184.2, C185.2, C186.2, C187.2, C188.2, C189.2, C190.2, C191.2, C192.2, C193.2, IC14.44 (VSS), IC14.58 (VSS), IC14.65 (VSS), IC15.4 (VSS), J16.P4 (GND), J16.P5 (GND), J16.P6 (GND), J16.P10 (GND), J16.P12 (GND), J16.S1 (GND), J16.S4 (GND), J16.S7 (GND), R122.2
GNDPWR: H11.1, H12.1
unnamed: C166.1, C168.1, IC14.53 (VSSOSC), Y5.2, Y5.4
unnamed: C166.2, IC14.52 (XI), R124.2, Y5.1
unnamed: C168.2, IC14.54 (XO), R124.1, Y5.3
unnamed: C170.1, IC14.4 (GRSTz), R125.2
unnamed: C188.1, C189.1, C190.1, C191.1, C192.1, C193.1, FB15.1, IC14.34 (VDDA33), IC14.40 (VDDA33), IC14.48 (VDDA33), IC14.62 (VDDA33)
unnamed: D22.1 (K), R132.2
unnamed: IC14.2 (PWM0), R132.1
unnamed: IC14.13 (GPIO4), R131.2
unnamed: IC14.17 (SPI_SCLK), IC15.6 (SCK)
unnamed: IC14.18 (SPI_DATA_OUT), IC15.5 (SI)
unnamed: IC14.20 (SPI_DATA_IN), IC15.2 (SO)
unnamed: IC14.21 (SPI_CS0), IC15.1 (~CE)
unnamed: IC14.23 (SPI_CS2/GPIO11), R126.1
unnamed: IC14.30 (FREQSEL0), R128.2
unnamed: IC14.31 (FREQSEL1), R127.1
unnamed: IC14.38 (USB_R1), R123.1
unnamed: IC14.39 (USB_R1RTN), R123.2
unnamed: IC14.50 (USB_VBUS), R121.1, R122.1
unnamed: IC15.3 (~WP), R130.2
unnamed: IC15.7 (~HOLD), R129.2
unnamed: J16.P1 (NC), R117.1
unnamed: J16.P2 (NC), R118.1
unnamed: J16.P3 (NC), R120.1
PORTA_DM: R119.1
PORTA_DP: R116.1
S1RX+: C165.1, J16.S6 (RXP)
S1RX-: C164.2, J16.S5 (RXN)
S1TX+: C163.1, J16.S3 (TXN)
S1TX-: C162.2, J16.S2 (TXP)
SATA1C+: IC14.36 (USB_DP), R116.2
SATA1C-: IC14.35 (USB_DM), R119.2
SATA1_RX+: C165.2, IC14.60 (SATA_RXP)
SATA1_RX-: C164.1, IC14.59 (SATA_RXM)
SATA1_TX+: C163.2, IC14.57 (SATA_TXP)
SATA1_TX-: C162.1, IC14.56 (SATA_TXM)

Notes on the sheet:
N.P.
40 MHz oscillator frequency selection
100 Ohm differential impedance 50 Ohm single ended impedance
Disk activity
WARNING: TX Polarity Swap !!! Select appropriate firmware version!
According to data sheet, VSSOSC should NOT be connected to GND!
!!! CRITICAL !!! This MUST be this exact flash, or one that supports 256bytes page writes with the 0x02 command!
This schematic follows roughly the reccommendations given in the TUSB9261 Implementation Guide https://www.ti.com/lit/pdf/slla315
