peterheinrich/ZHAW_DFF_RPI_Network_Lab_Board/ecad/SD_MMC.sch

## KiCad design ecad/SD_MMC.sch (2020-12-07)

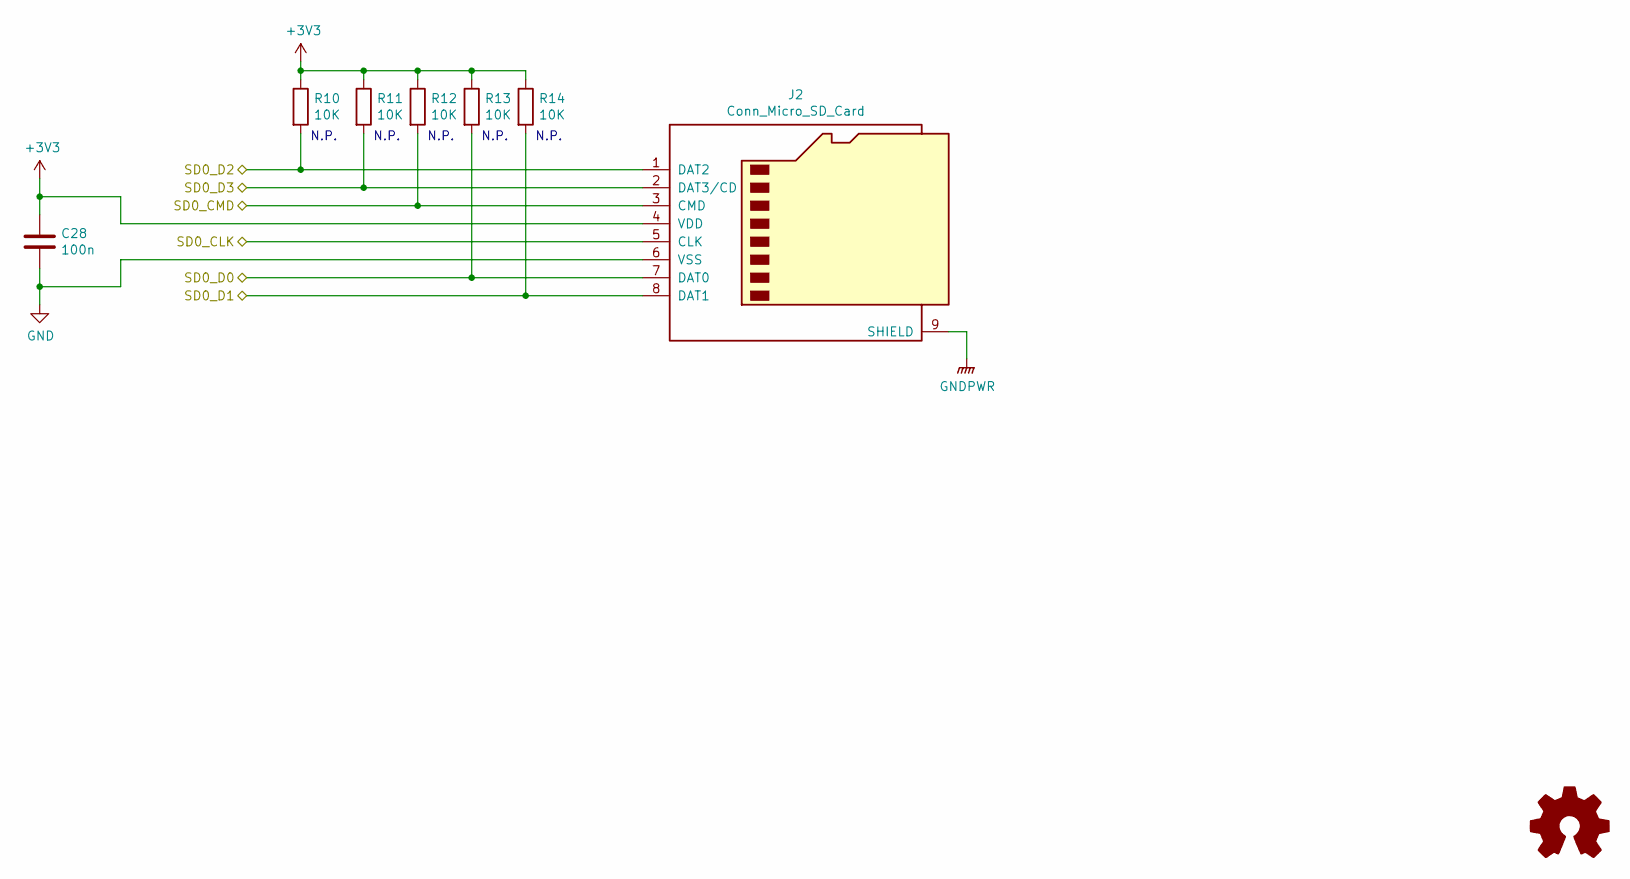
[picture p48: schematic SD_MMC.sch]

Parts:
C28: 100n; C_0603_1608Metric; MPN C0603C104M4RACTU
J2: Conn_Micro_SD_Card; 693071010811; MPN 693071010811
R10, R11, R12, R13, R14: 10K; R_0603_1608Metric; MPN CRCW060310K0FKEA

Connections:
+3V3: C28.1, J2.4 (VDD), R10.1, R11.1, R12.1, R13.1, R14.1
GND: C28.2, J2.6 (VSS)
GNDPWR: J2.9 (SHIELD)
SD0_CLK: J2.5 (CLK)
SD0_CMD: J2.3 (CMD), R12.2
SD0_D0: J2.7 (DAT0), R13.2
SD0_D1: J2.8 (DAT1), R14.2
SD0_D2: J2.1 (DAT2), R10.2
SD0_D3: J2.2 (DAT3/CD), R11.2

Notes on the sheet:
N.P.
