peterheinrich/ZHAW_DFF_RPI_Network_Lab_Board/ecad/SYSCTRL.sch

## KiCad design ecad/SYSCTRL.sch (2020-12-07)

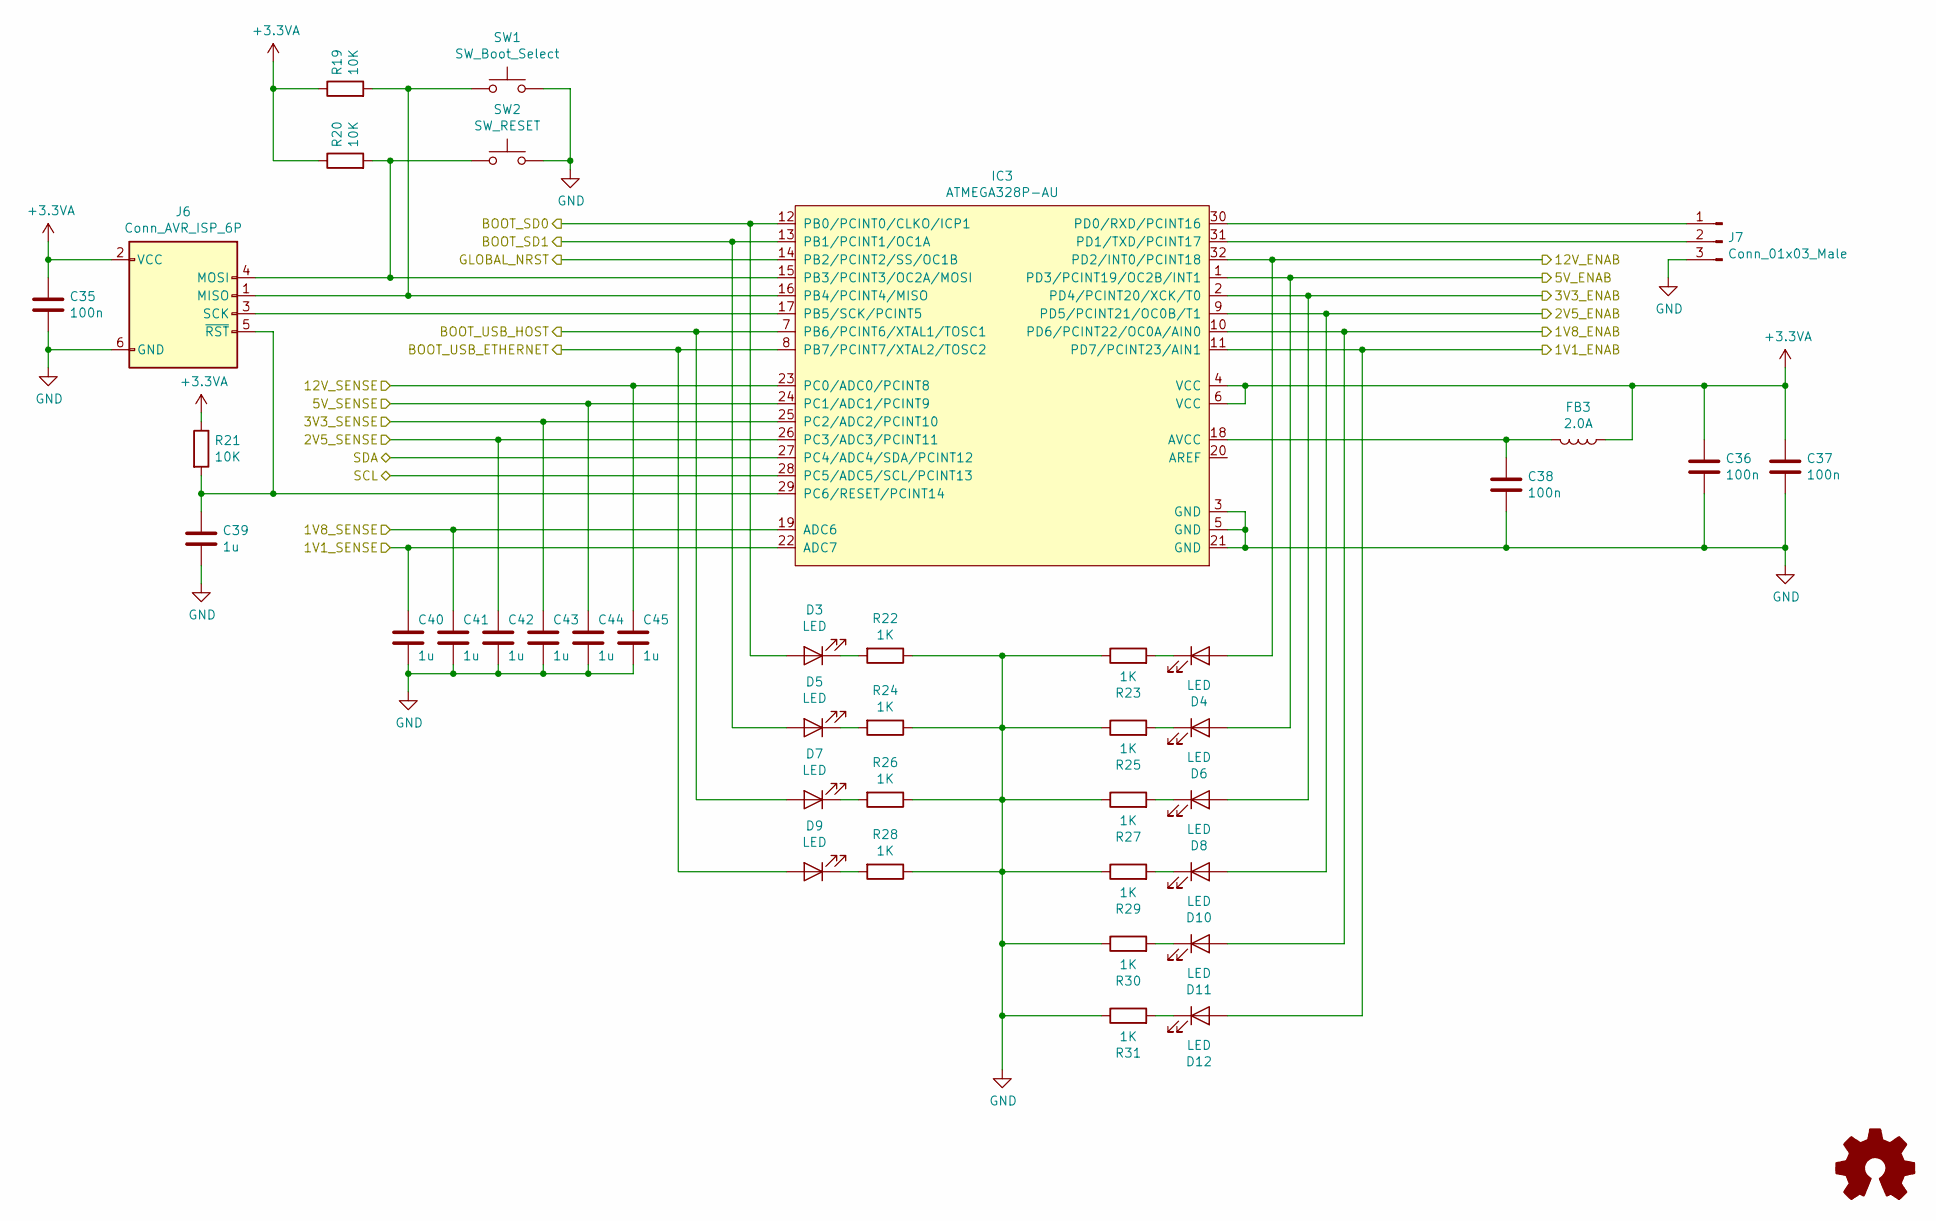
[picture p49: schematic SYSCTRL.sch]

Parts:
C35, C36, C37, C38: 100n; C_0603_1608Metric; MPN C0603C104M4RACTU
C39, C40, C41, C42, C43, C44, C45: 1u; C_0805_2012Metric; MPN C0805C105K3PACTU
D3, D4, D5, D6, D7, D8, D9, D10, D11, D12: LED; LED_0805_2012Metric_Pad1.15x1.40mm_HandSolder; MPN KP-2012LSGC
FB3: 2.0A; L_0603_1608Metric_Pad1.05x0.95mm_HandSolder; MPN BLM18PG121SN1D
IC3: ATMEGA328P-AU; TQFP-32_7x7mm_P0.8mm; MPN ATMEGA328P-AU
J6: Conn_AVR_ISP_6P; PinHeader_2x03_P2.54mm_Vertical; MPN 826942-3
J7: Conn_01x03_Male; PinHeader_1x03_P2.54mm_Vertical; MPN 826629-3
R19, R20, R21: 10K; R_0603_1608Metric; MPN CRCW060310K0FKEA
R22, R23, R24, R25, R26, R27, R28, R29, R30, R31: 1K; R_0603_1608Metric; MPN CRCW06031K00FKEA
SW1: SW_Boot_Select; SW_Push_1P1T_NO_6x6mm_H9.5mm; MPN PTS645SM43SMTR92LFS
SW2: SW_RESET; SW_Push_1P1T_NO_6x6mm_H9.5mm; MPN PTS645SM43SMTR92LFS

Connections:
1V1_ENAB: D12.2 (A), IC3.11 (PD7/PCINT23/AIN1)
1V1_SENSE: C40.1, IC3.22 (ADC7)
1V8_ENAB: D11.2 (A), IC3.10 (PD6/PCINT22/OC0A/AIN0)
1V8_SENSE: C41.1, IC3.19 (ADC6)
2V5_ENAB: D10.2 (A), IC3.9 (PD5/PCINT21/OC0B/T1)
2V5_SENSE: C42.1, IC3.26 (PC3/ADC3/PCINT11)
3V3_ENAB: D8.2 (A), IC3.2 (PD4/PCINT20/XCK/T0)
3V3_SENSE: C43.1, IC3.25 (PC2/ADC2/PCINT10)
5V_ENAB: D6.2 (A), IC3.1 (PD3/PCINT19/OC2B/INT1)
5V_SENSE: C44.1, IC3.24 (PC1/ADC1/PCINT9)
12V_ENAB: D4.2 (A), IC3.32 (PD2/INT0/PCINT18)
12V_SENSE: C45.1, IC3.23 (PC0/ADC0/PCINT8)
+3.3VA: C35.1, C36.1, C37.1, FB3.1, IC3.4 (VCC), IC3.6 (VCC), J6.2 (VCC), R19.1, R20.1, R21.1
BOOT_SD0: D3.2 (A), IC3.12 (PB0/PCINT0/CLKO/ICP1)
BOOT_SD1: D5.2 (A), IC3.13 (PB1/PCINT1/OC1A)
BOOT_USB_ETHERNET: D9.2 (A), IC3.8 (PB7/PCINT7/XTAL2/TOSC2)
BOOT_USB_HOST: D7.2 (A), IC3.7 (PB6/PCINT6/XTAL1/TOSC1)
GLOBAL_NRST: IC3.14 (PB2/PCINT2/SS/OC1B)
GND: C35.2, C36.2, C37.2, C38.2, C39.2, C40.2, C41.2, C42.2, C43.2, C44.2, C45.2, IC3.3 (GND), IC3.5 (GND), IC3.21 (GND), J6.6 (GND), J7.3, R22.1, R23.1, R24.1, R25.1, R26.1, R27.1, R28.1, R29.1, R30.1, R31.1, SW1.2, SW2.2
unnamed: C38.1, FB3.2, IC3.18 (AVCC)
unnamed: C39.1, IC3.29 (PC6/RESET/PCINT14), J6.5 (~RST), R21.2
unnamed: D3.1 (K), R22.2
unnamed: D4.1 (K), R23.2
unnamed: D5.1 (K), R24.2
unnamed: D6.1 (K), R25.2
unnamed: D7.1 (K), R26.2
unnamed: D8.1 (K), R27.2
unnamed: D9.1 (K), R28.2
unnamed: D10.1 (K), R29.2
unnamed: D11.1 (K), R30.2
unnamed: D12.1 (K), R31.2
unnamed: IC3.15 (PB3/PCINT3/OC2A/MOSI), J6.4 (MOSI), R20.2, SW2.1
unnamed: IC3.16 (PB4/PCINT4/MISO), J6.1 (MISO), R19.2, SW1.1
unnamed: IC3.17 (PB5/SCK/PCINT5), J6.3 (SCK)
unnamed: IC3.30 (PD0/RXD/PCINT16), J7.1
unnamed: IC3.31 (PD1/TXD/PCINT17), J7.2
SCL: IC3.28 (PC5/ADC5/SCL/PCINT13)
SDA: IC3.27 (PC4/ADC4/SDA/PCINT12)
