peterheinrich/ZHAW_DFF_RPI_Network_Lab_Board/ecad/USBConsole.sch

## KiCad design ecad/USBConsole.sch (2020-12-07)

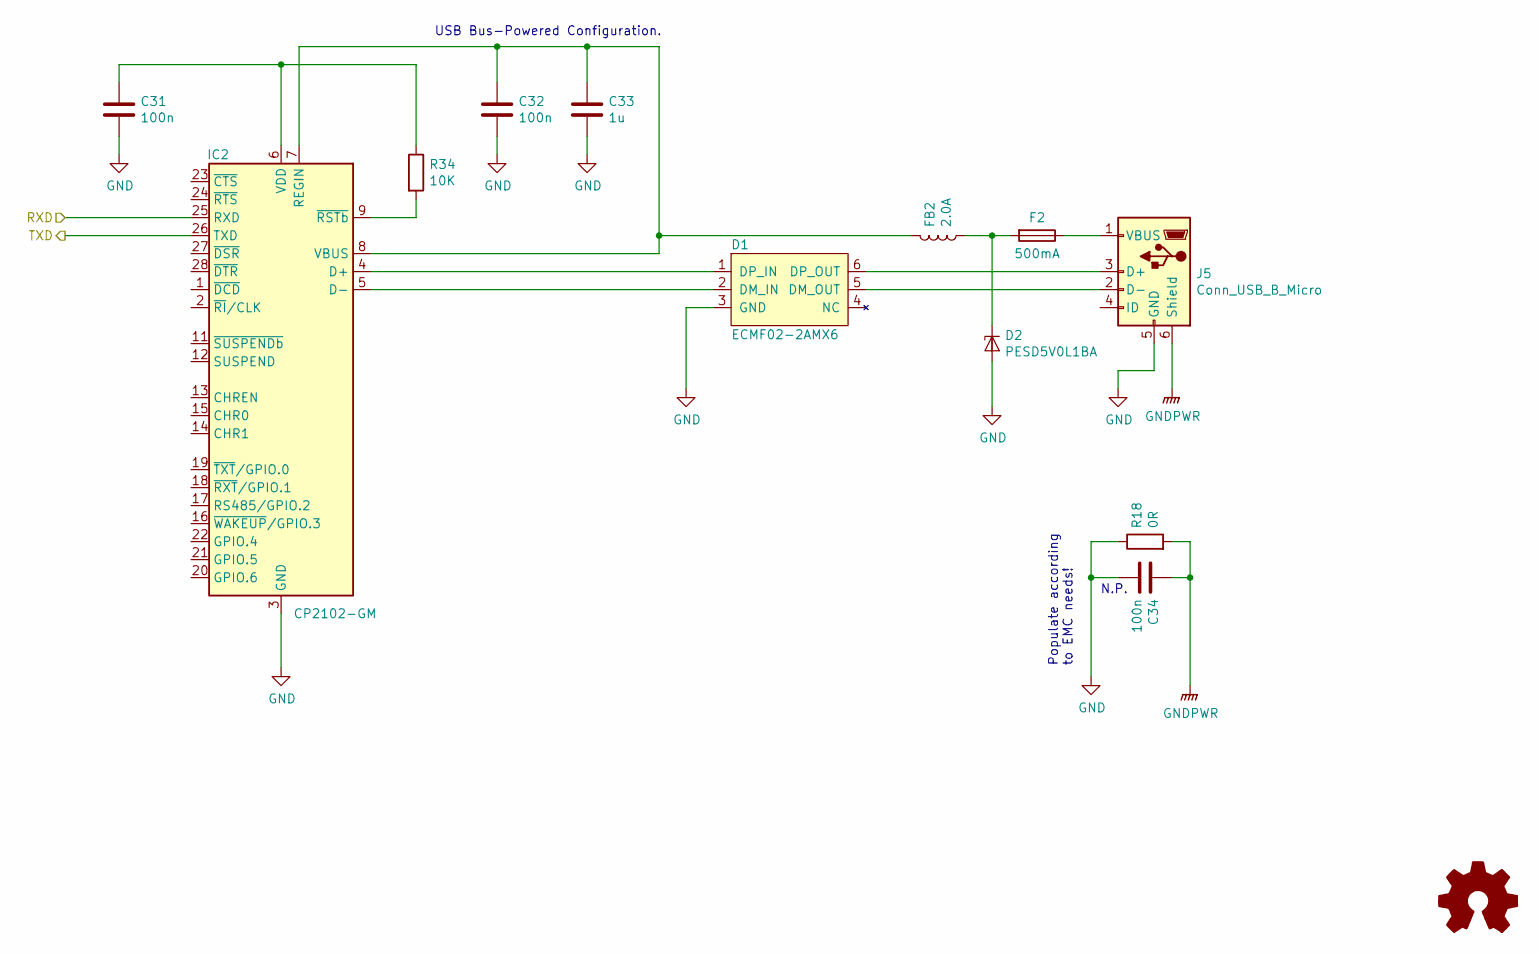
[picture p50: schematic USBConsole.sch]

Parts:
C31, C32: 100n; C_0603_1608Metric; MPN C0603C104M4RACTU
C33: 1u; C_0805_2012Metric; MPN C0805C105K3PACTU
C34: 100n; C_0805_2012Metric; MPN C0805C104K5RACTU
D1: ECMF02-2AMX6; ST_UQFN-6L_1.5x1.7mm_Pitch0.5mm; MPN ECMF02-2AMX6
D2: PESD5V0L1BA; D_SOD-323_HandSoldering; MPN PESD5V0L1BA,115
F2: 500mA; Fuse_1206_3216Metric; MPN 1206L050YR
FB2: 2.0A; L_0603_1608Metric_Pad1.05x0.95mm_HandSolder; MPN BLM18PG121SN1D
IC2: CP2102-GM; QFN-28-1EP_5x5mm_P0.5mm_EP3.35x3.35mm; MPN CP2102-GM
J5: Conn_USB_B_Micro; USB_Micro-B_Molex-105017-0001; MPN 105017-0001
R18: 0R; R_0805_2012Metric; MPN CRCW08050000Z0EA
R34: 10K; R_0603_1608Metric; MPN CRCW060310K0FKEA

Connections:
GND: C31.2, C32.2, C33.2, C34.2, D1.3 (GND), D2.2 (A), IC2.3 (GND), IC2.29 (GND), J5.5 (GND), R18.1
GNDPWR: C34.1, J5.6 (Shield), R18.2
unnamed: C31.1, IC2.6 (VDD), R34.1
unnamed: C32.1, C33.1, FB2.2, IC2.7 (REGIN), IC2.8 (VBUS)
unnamed: D1.1 (DP_IN), IC2.4 (D+)
unnamed: D1.2 (DM_IN), IC2.5 (D-)
unnamed: D1.5 (DM_OUT), J5.2 (D-)
unnamed: D1.6 (DP_OUT), J5.3 (D+)
unnamed: D2.1 (K1), F2.2, FB2.1
unnamed: F2.1, J5.1 (VBUS)
unnamed: IC2.9 (~RSTb), R34.2
RXD: IC2.25 (RXD)
TXD: IC2.26 (TXD)

Notes on the sheet:
USB Bus-Powered Configuration.
Populate according to EMC needs!
N.P.
