peterheinrich/ZHAW_DFF_RPI_Network_Lab_Board/ecad/USB_HOST0.sch

## KiCad design ecad/USB_HOST0.sch (2020-12-07)

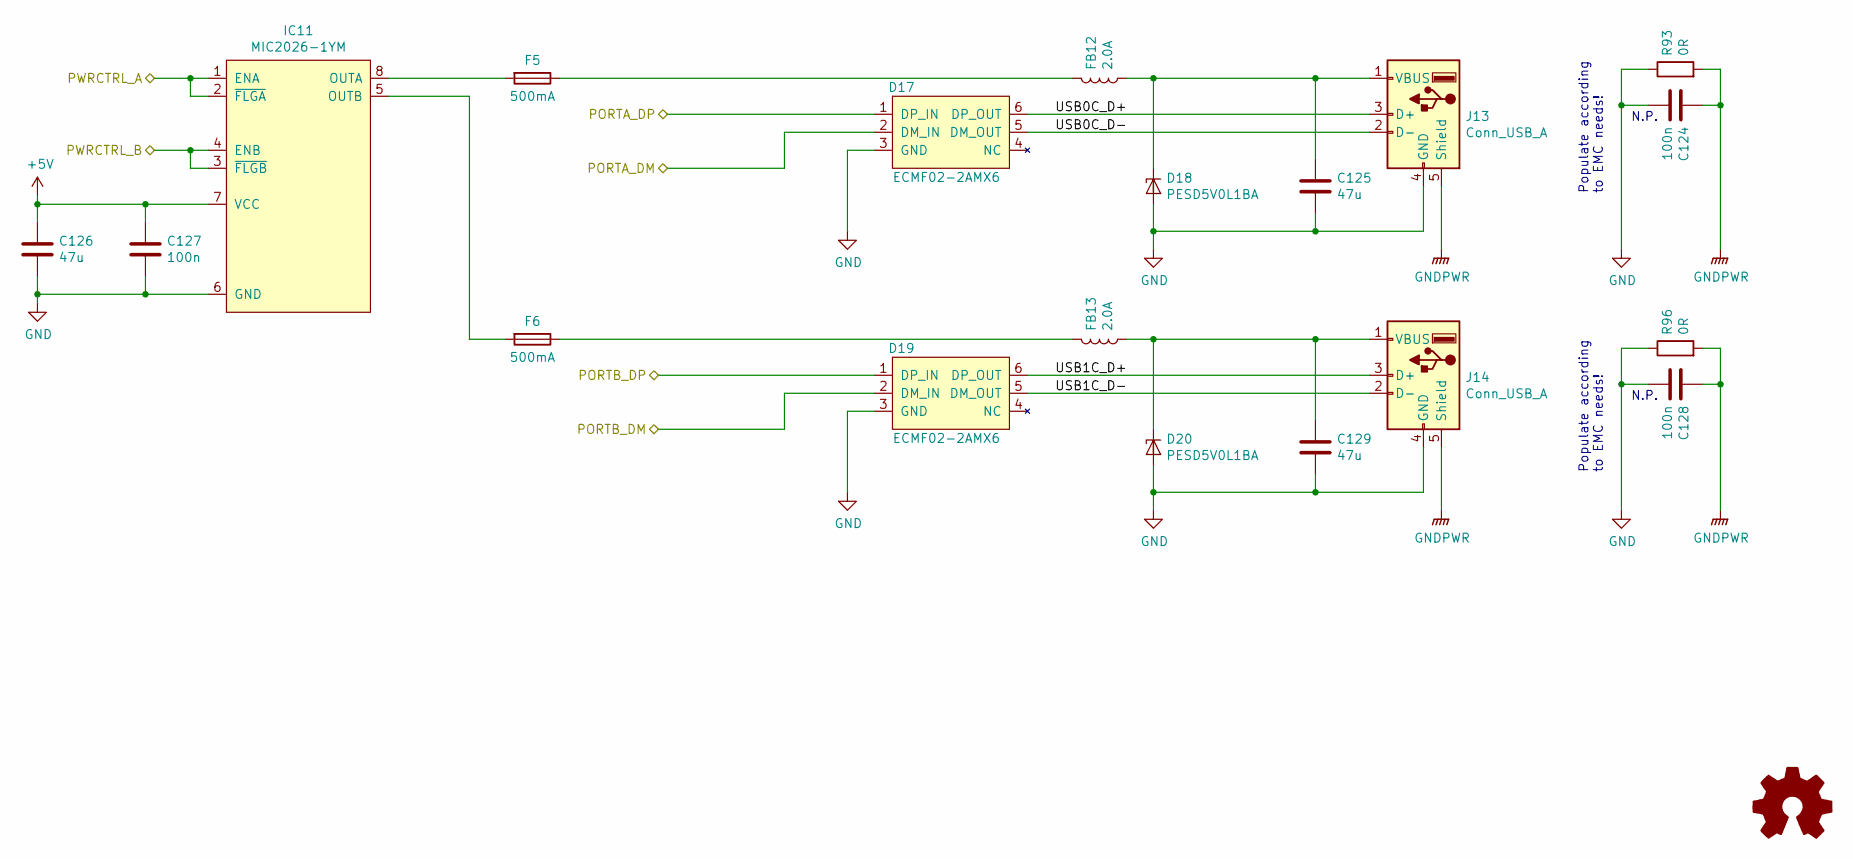
[picture p51: schematic USB_HOST0.sch]

Parts:
C124, C128: 100n; C_0805_2012Metric; MPN C0805C104K5RACTU
C125, C126, C129: 47u; C_0805_2012Metric; MPN GRM21BR60J476ME15L
C127: 100n; C_0603_1608Metric; MPN C0603C104M4RACTU
D17, D19: ECMF02-2AMX6; ST_UQFN-6L_1.5x1.7mm_Pitch0.5mm; MPN ECMF02-2AMX6
D18, D20: PESD5V0L1BA; D_SOD-323_HandSoldering; MPN PESD5V0L1BA,115
F5, F6: 500mA; Fuse_1206_3216Metric; MPN 1206L050YR
FB12, FB13: 2.0A; L_0603_1608Metric_Pad1.05x0.95mm_HandSolder; MPN BLM18PG121SN1D
IC11: MIC2026-1YM; SOIC-8_3.9x4.9mm_P1.27mm; MPN MIC2026-1YM
J13, J14: Conn_USB_A; 73725-0110BLF; MPN 73725-0110BLF
R93, R96: 0R; R_0805_2012Metric; MPN CRCW08050000Z0EA

Connections:
+5V: C126.1, C127.1, IC11.7 (VCC)
GND: C124.2, C125.2, C126.2, C127.2, C128.2, C129.2, D17.3 (GND), D18.2 (A), D19.3 (GND), D20.2 (A), IC11.6 (GND), J13.4 (GND), J14.4 (GND), R93.1, R96.1
GNDPWR: C124.1, C128.1, J13.5 (Shield), J14.5 (Shield), R93.2, R96.2
unnamed: C125.1, D18.1 (K1), FB12.1, J13.1 (VBUS)
unnamed: C129.1, D20.1 (K1), FB13.1, J14.1 (VBUS)
unnamed: F5.1, FB12.2
unnamed: F5.2, IC11.8 (OUTA)
unnamed: F6.1, FB13.2
unnamed: F6.2, IC11.5 (OUTB)
PORTA_DM: D17.2 (DM_IN)
PORTA_DP: D17.1 (DP_IN)
PORTB_DM: D19.2 (DM_IN)
PORTB_DP: D19.1 (DP_IN)
PWRCTRL_A: IC11.1 (ENA), IC11.2 (~FLGA)
PWRCTRL_B: IC11.3 (~FLGB), IC11.4 (ENB)
USB0C_D+: D17.6 (DP_OUT), J13.3 (D+)
USB0C_D-: D17.5 (DM_OUT), J13.2 (D-)
USB1C_D+: D19.6 (DP_OUT), J14.3 (D+)
USB1C_D-: D19.5 (DM_OUT), J14.2 (D-)

Notes on the sheet:
Populate according to EMC needs!
N.P.
