peterheinrich/ZHAW_DFF_RPI_Network_Lab_Board/ecad/WLAN0.sch

## KiCad design ecad/WLAN0.sch (2020-12-07)

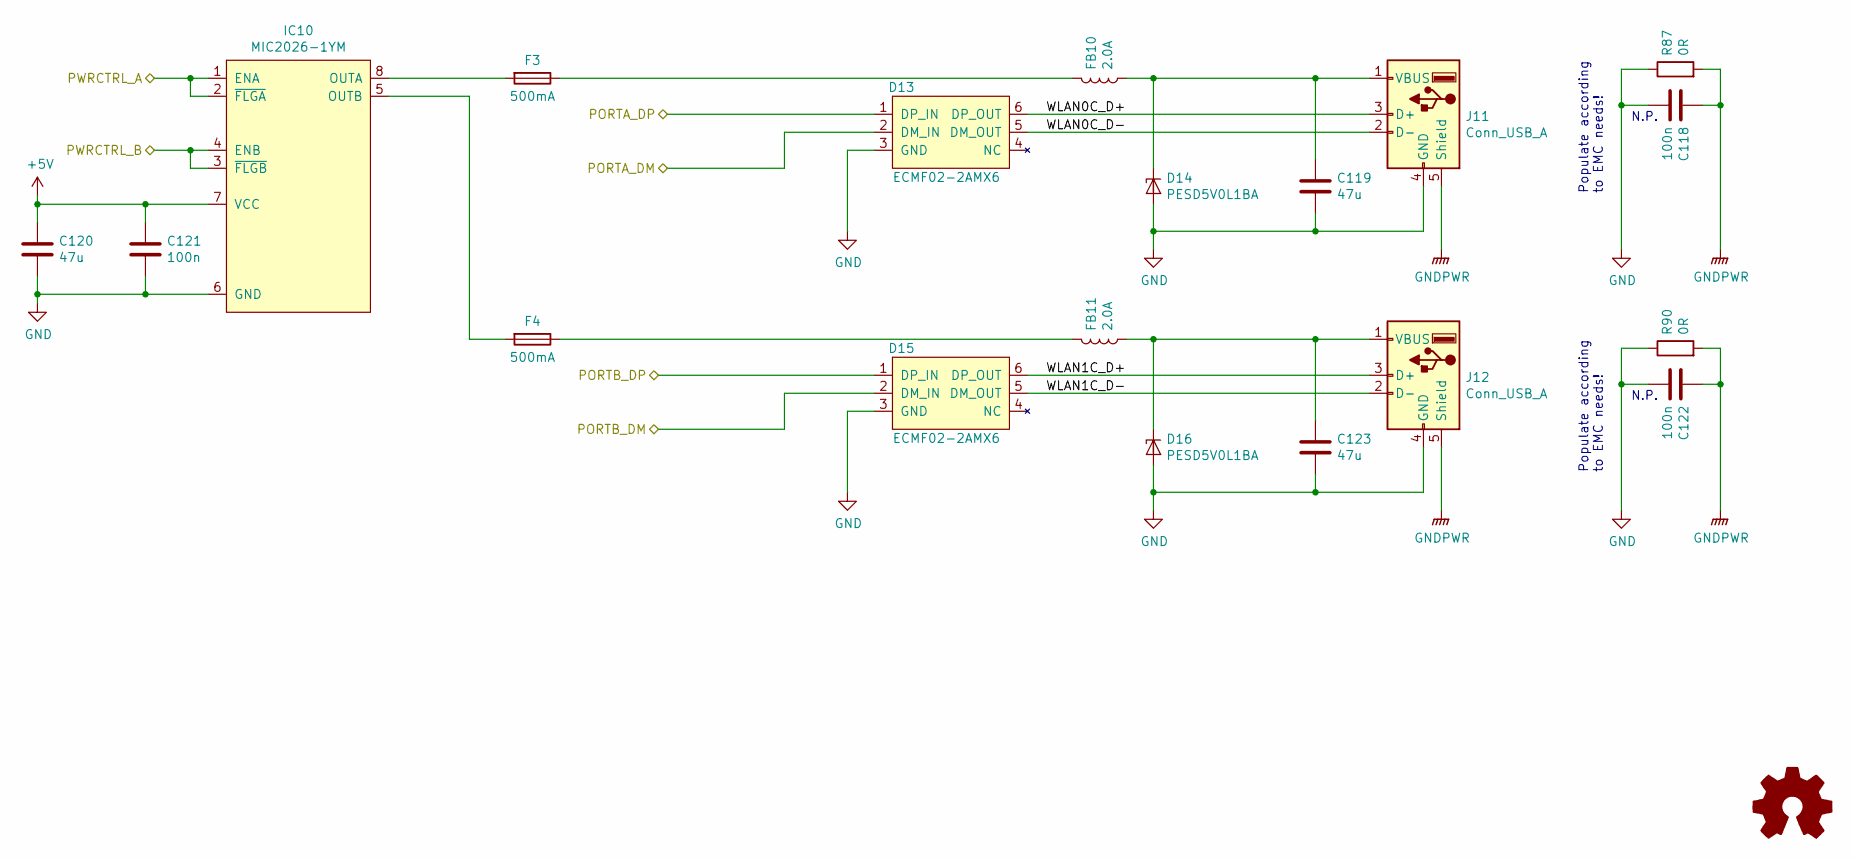
[picture p52: schematic WLAN0.sch]

Parts:
C118, C122: 100n; C_0805_2012Metric; MPN C0805C104K5RACTU
C119, C120, C123: 47u; C_0805_2012Metric; MPN GRM21BR60J476ME15L
C121: 100n; C_0603_1608Metric; MPN C0603C104M4RACTU
D13, D15: ECMF02-2AMX6; ST_UQFN-6L_1.5x1.7mm_Pitch0.5mm; MPN ECMF02-2AMX6
D14, D16: PESD5V0L1BA; D_SOD-323_HandSoldering; MPN PESD5V0L1BA,115
F3, F4: 500mA; Fuse_1206_3216Metric; MPN 1206L050YR
FB10, FB11: 2.0A; L_0603_1608Metric_Pad1.05x0.95mm_HandSolder; MPN BLM18PG121SN1D
IC10: MIC2026-1YM; SOIC-8_3.9x4.9mm_P1.27mm; MPN MIC2026-1YM
J11, J12: Conn_USB_A; 73725-0110BLF; MPN 73725-0110BLF
R87, R90: 0R; R_0805_2012Metric; MPN CRCW08050000Z0EA

Connections:
+5V: C120.1, C121.1, IC10.7 (VCC)
GND: C118.2, C119.2, C120.2, C121.2, C122.2, C123.2, D13.3 (GND), D14.2 (A), D15.3 (GND), D16.2 (A), IC10.6 (GND), J11.4 (GND), J12.4 (GND), R87.1, R90.1
GNDPWR: C118.1, C122.1, J11.5 (Shield), J12.5 (Shield), R87.2, R90.2
unnamed: C119.1, D14.1 (K1), FB10.1, J11.1 (VBUS)
unnamed: C123.1, D16.1 (K1), FB11.1, J12.1 (VBUS)
unnamed: F3.1, FB10.2
unnamed: F3.2, IC10.8 (OUTA)
unnamed: F4.1, FB11.2
unnamed: F4.2, IC10.5 (OUTB)
PORTA_DM: D13.2 (DM_IN)
PORTA_DP: D13.1 (DP_IN)
PORTB_DM: D15.2 (DM_IN)
PORTB_DP: D15.1 (DP_IN)
PWRCTRL_A: IC10.1 (ENA), IC10.2 (~FLGA)
PWRCTRL_B: IC10.3 (~FLGB), IC10.4 (ENB)
WLAN0C_D+: D13.6 (DP_OUT), J11.3 (D+)
WLAN0C_D-: D13.5 (DM_OUT), J11.2 (D-)
WLAN1C_D+: D15.6 (DP_OUT), J12.3 (D+)
WLAN1C_D-: D15.5 (DM_OUT), J12.2 (D-)

Notes on the sheet:
Populate according to EMC needs!
N.P.
